fabkury/p64/firmware/assets/fonts/digital-display/Digital-Display-Info.md

# Digital Display
Digital Display is a 19x15 pixel font designed to mimic digital clock fonts while having a bit more flexability in design.

## Author
[VEXED](https://v3x3d.itch.io/)

## Basic Info
- Base Glyph Height: 19px
- Scales: 19, 38, 57, 76, etc.
- Ascender Max: 8px
- Descender Max: 6px

## Kerning
``
``

## License
[Creative Commons Attribution v4.0 International](https://creativecommons.org/licenses/by/4.0/deed.en)

## Supported Glyphs (PNG Order)
``
ABCDEFGH
IJKLMNOP
QRSTUVWX
YZ
abcdefgh
ijklmnop
qrstuvwx
yz
01234567
89
 !"#$%&'
()*+,-./
:;<=>?[]
\^_`{}|~
@∎
ÄÁÀÂÅÃÇç
äáàâåãÑñ
ÏÍÌÎÜÚÙÛ
ïíìîüúùû
ÖÓÒÔÕŸÝỲ
öóòôõÿýỳ
ËÉÈÊëéèê
ÆæßðÐþÞ
¿¡Œœ
``
