fabkury/p64/firmware/assets/fonts/everyday-standard/Everyday-Standard-Info.md

# Everyday Standard
Everyday Standard is a 6pt pixel art font that is part of my Everyday font series. Everyday fonts are designed to be clear and legible at a wide variety of sizes (Everyday Standard's size being the in the middle).

## Author
[VEXED](https://v3x3d.itch.io/)

## Basic Info
- Base Glyph Height: 6px
- Scales: 6, 12, 18, 24, etc
- Ascender Max: 3px
- Descender Max: 2px

## Kerning
None

## License
[Creative Commons Attribution v4.0 International](https://creativecommons.org/licenses/by/4.0/deed.en)

## Supported Glyphs (PNG Order)
``
ABCDEFGH
IJKLMNOP
QRSTUVWX
YZ
abcdefgh
ijklmnop
qrstuvwx
yz
01234567
89
 !"#$%&'
()*+,-./
:;<=>?[]
\^_`{}|~
@∎
ÄÁÀÂÅÃÇç
äáàâåãÑñ
ÏÍÌÎÜÚÙÛ
ïíìîüúùû
ÖÓÒÔÕŸÝỲ
öóòôõÿýỳ
ËÉÈÊëéèê
ÆæßðÐþÞ
¿¡Œœ
АаБбВвГг
ҐґДдЕеЄє
ЖжЗзИиІі
ЇїЙйКкЛл
МмНнОоПп
РрСсТтУу
ФфХхЦцЧч
ШшЩщЬьЮю
ЯяЭэЫыЁё
ЪъӨөӘәҒғ
ҚқҢңҰұҺһ
Үү
Øø
‽⸘ĞğıŞşİ
ĄąĘęŁłŚś
ĆćŻżŹźŃń
ſ́
←↑→↓↔↕
↖↗↘↙
``
