fabkury/p64/firmware/assets/fonts/extra-thick/Extra-Thick-Info.md

# Extra Thick
Extra Thick is a bold 17pt pixel art font designed with very wide and thick looking lettering. 

## Author
[VEXED](https://v3x3d.itch.io/)

## Basic Info
- Base Glyph Height: 17px
- Scales: 17, 34, 51, 68, etc
- Ascender Max: 12px
- Descender Max: 5px

## Kerning
None

## License
[Creative Commons Attribution v4.0 International](https://creativecommons.org/licenses/by/4.0/deed.en)

## Supported Glyphs (PNG Order)
``
ABCDEFGH
IJKLMNOP
QRSTUVWX
YZ
abcdefgh
ijklmnop
qrstuvwx
yz
01234567
89
 !"#$%&'
()*+,-./
:;<=>?[]
\^_`{}|~
@∎
ÄÁÀÂÅÃÇç
äáàâåãÑñ
ÏÍÌÎÜÚÙÛ
ïíìîüúùû
ÖÓÒÔÕŸÝỲ
öóòôõÿýỳ
ËÉÈÊëéèê
ÆæßðÐþÞ
¿¡Œœ
``
