fabkury/p64/firmware/assets/fonts/capital-hill/Capital-Hill-Info.md

# Capital Hill
Capital Hill is a 6pt pixel art font with a focus on capital lettering. Capital Hill's lowercase lettering is styled as scaled down uppercase characters, keeping the two cases subtly distinguished.

## Author
[VEXED](https://v3x3d.itch.io/)

## Basic Info
- Base Glyph Height: 6px
- Scales: 6, 12, 18, 24, etc
- Ascender Max: 3px
- Descender Max: 1px

## Kerning
None

## License
[Creative Commons Attribution v4.0 International](https://creativecommons.org/licenses/by/4.0/deed.en)

## Notes
Turkish support on an all capital lettering font is a touch complex because of the 4 "i" glyphs that exist, please see below for how I have formatted it to work on Capital Hill.

For Capital Hill I have kept the Latin capital set for both uppercase and lowercase consistent. To add the Turkish dotted "i" variations I have made the capital dotted Turkish "i" and the lowercase no dot Turkish "i" both have dots. This allows for accommodation of all 4 glyphs while not compromising on the capital letter style of Capital Hill.

## Supported Glyphs (PNG Order)
``
ABCDEFGH
IJKLMNOP
QRSTUVWX
YZ
abcdefgh
ijklmnop
qrstuvwx
yz
01234567
89
 !"#$%&'
()*+,-./
:;<=>?[]
\^_`{}|~
@∎…‹›
«»■█▀▄©®
═║╗╝╔╚╣╠
╩╦╬─│┐┘┌
└┤├┴┬┼§¶
¤¢¥£€₽฿₣
°×÷≡µ±ƒ¬
Ææ¿¡¦░▒▓
ºª¹²³½⅔¾
¼⅓⅕⅖⅗⅘⅙⅚
⅛⅜⅝⅞“”‘’
ÄÁÀÂÅÃÇç
äáàâåãÑñ
ÏÍÌÎÜÚÙÛ
ïíìîüúùû
ÖÓÒÔÕŸÝỲ
öóòôõÿýỳ
ËÉÈÊëéèê
ŒœßðÐþÞ
АаБбВвГг
ҐґДдЕеЄє
ЖжЗзИиІі
ЇїЙйКкЛл
МмНнОоПп
РрСсТтУу
ФфХхЦцЧч
ШшЩщЬьЮю
ЯяЭэЫыЁё
ЪъӨөӘәҒғ
ҚқҢңҰұҺһ
Үү
Øø
‽⸘ĞğıŞşİ
ĄąĘęŁłŚś
ĆćŻżŹźŃń
ſ́
←↑→↓↔↕
↖↗↘↙
``
