fabkury/p64/docs/images/photos/p64-brick-wall-analogue-clock.jpg

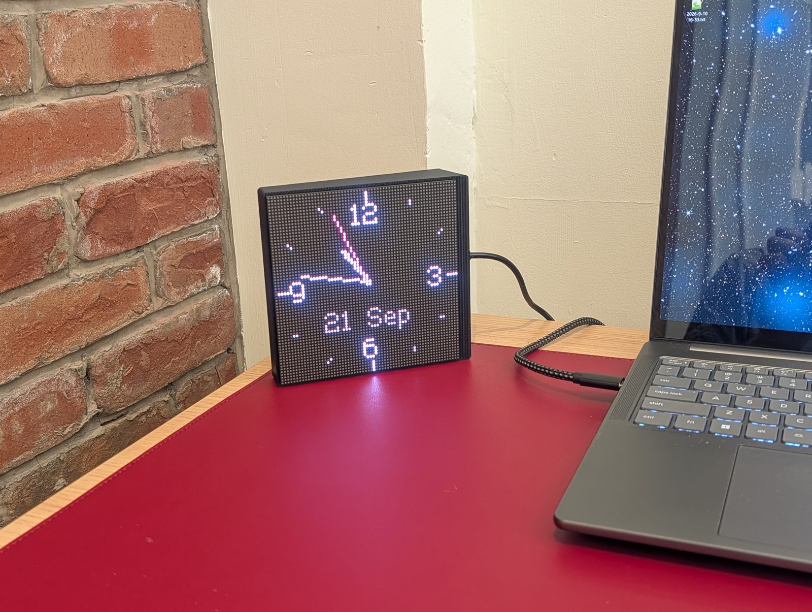
docs/images/photos/p64-brick-wall-analogue-clock.jpg
