fabkury/p64/docs/images/photos/p64-brick-wall-artwork-dark.jpg

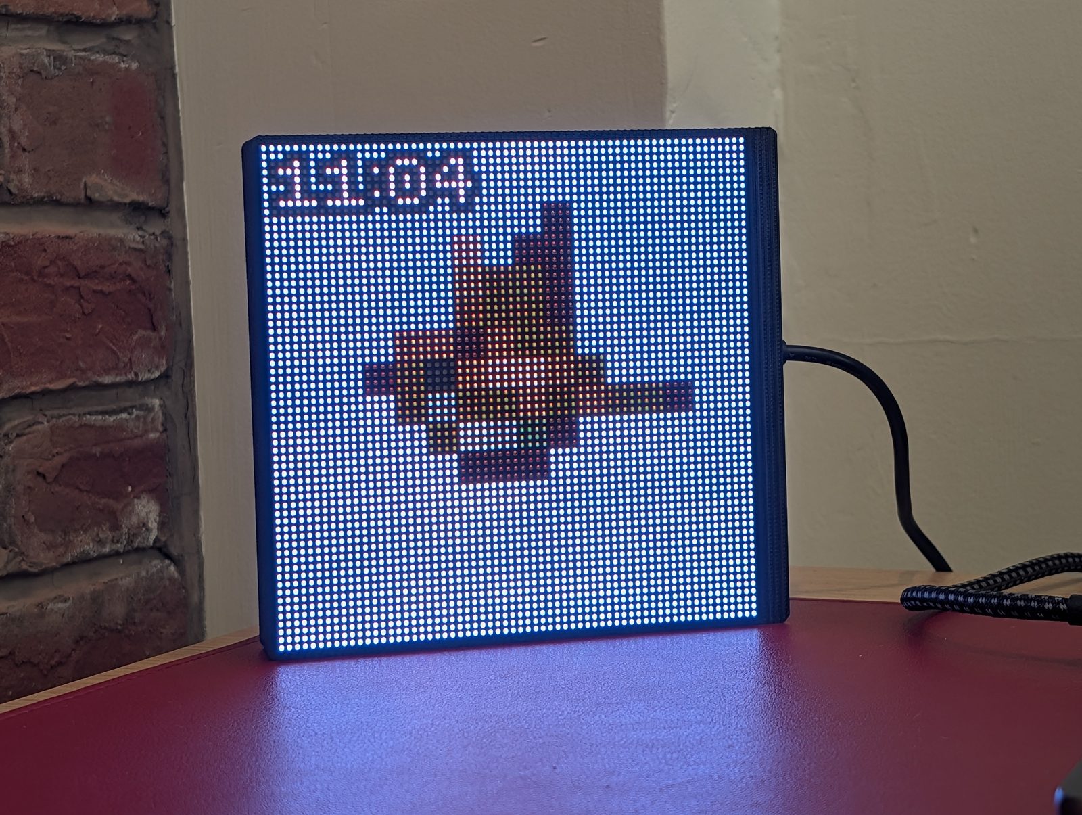
docs/images/photos/p64-brick-wall-artwork-dark.jpg
