fabkury/p64/docs/images/photos/p64-brick-wall-artwork-green.jpg

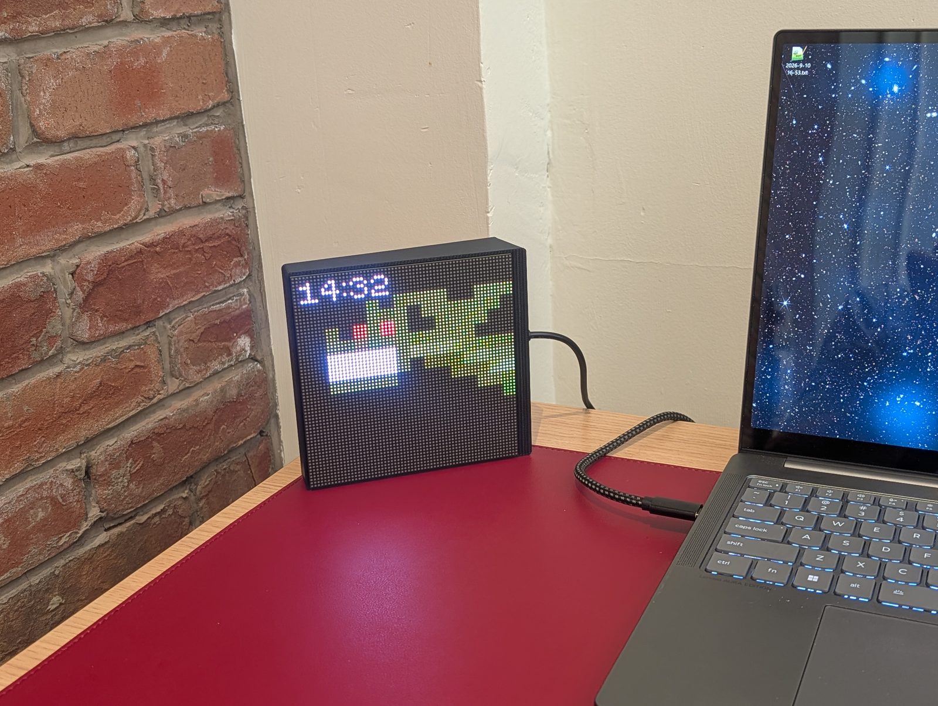
docs/images/photos/p64-brick-wall-artwork-green.jpg
