fabkury/p64/docs/images/photos/p64-brick-wall-heart.jpg

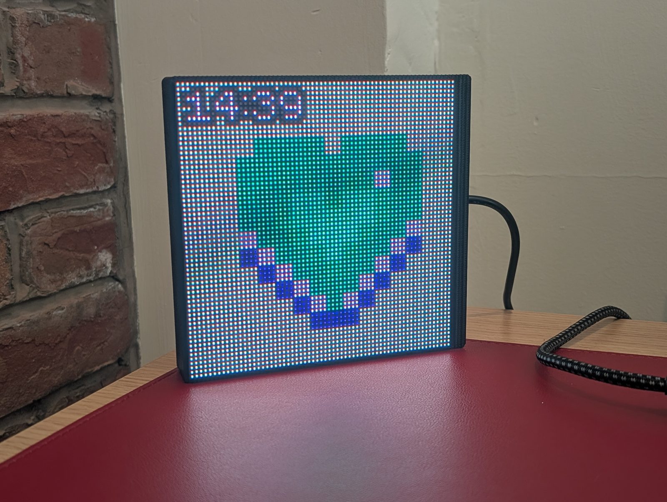
docs/images/photos/p64-brick-wall-heart.jpg
