fabkury/p64/docs/images/photos/p64-brick-wall-jellyfish.jpg

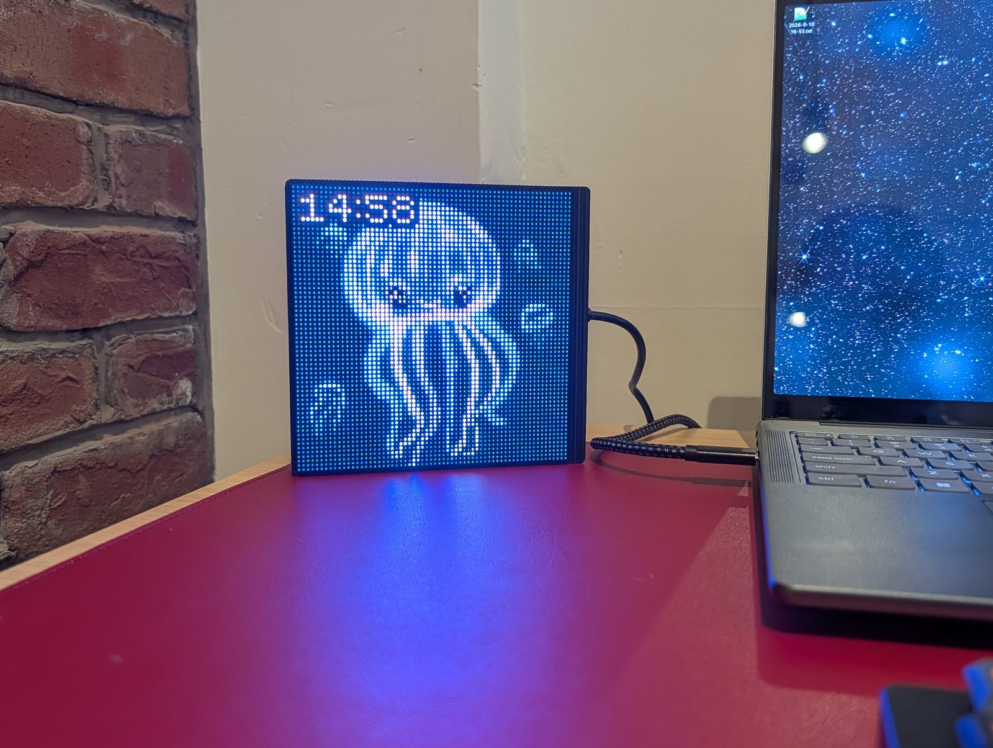
docs/images/photos/p64-brick-wall-jellyfish.jpg
