fabkury/p64/docs/images/photos/p64-shell-back.jpg

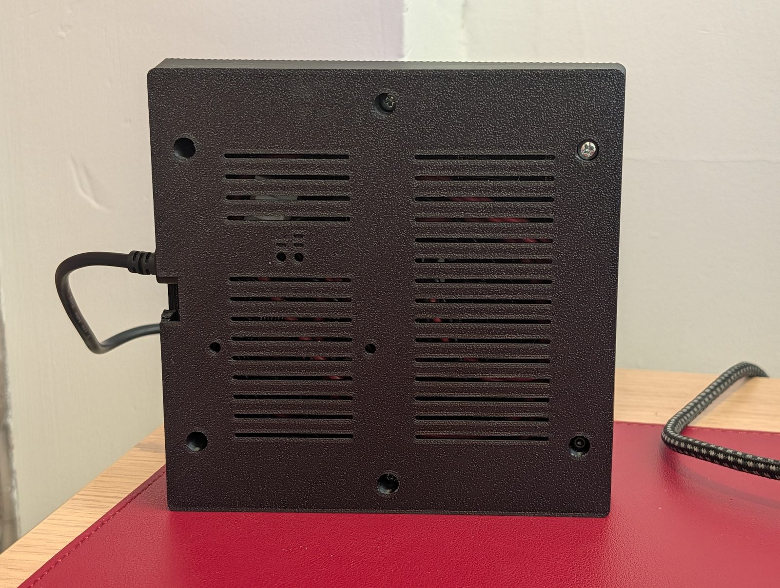
docs/images/photos/p64-shell-back.jpg
