fabkury/p64/docs/images/photos/p64-shell-side.jpg

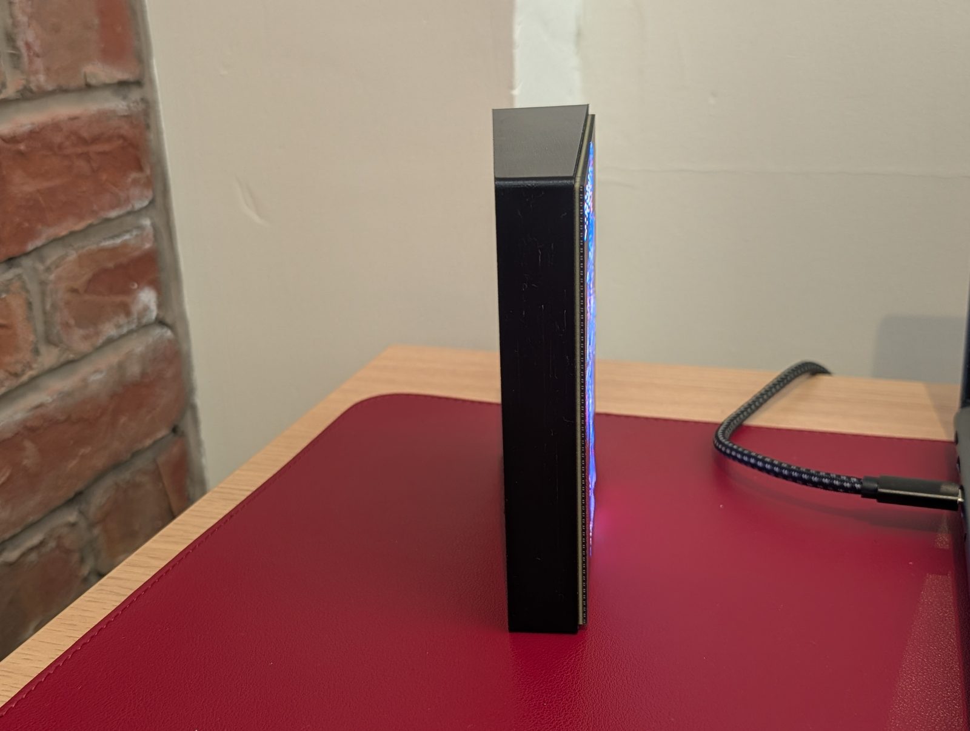
docs/images/photos/p64-shell-side.jpg
