fabkury/p64/docs/images/photos/p64-shell-v1-back-vents.jpg

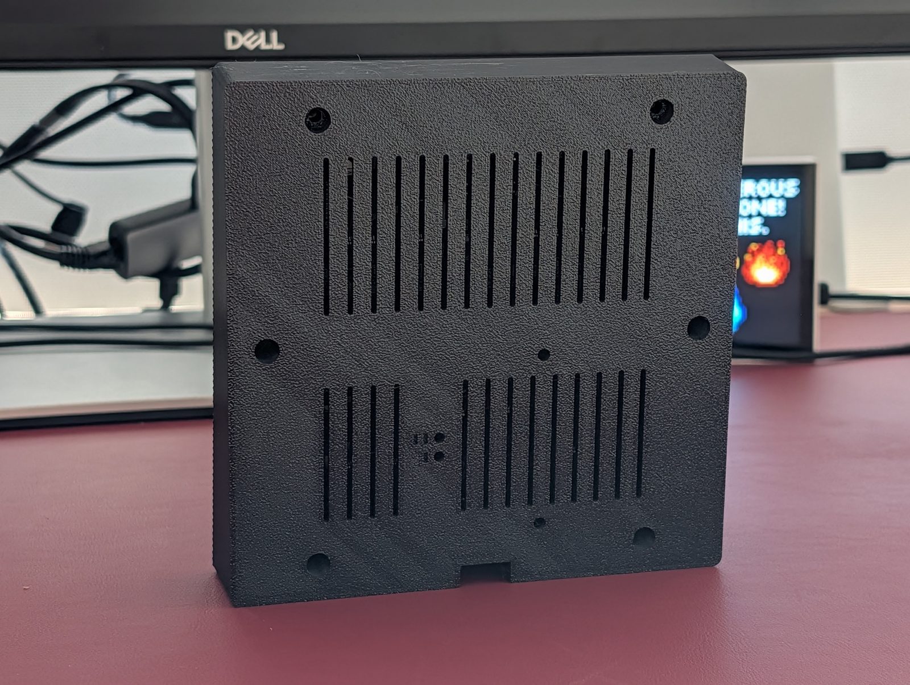
docs/images/photos/p64-shell-v1-back-vents.jpg
