fabkury/p64/firmware/docs/design/air-widget/european.png

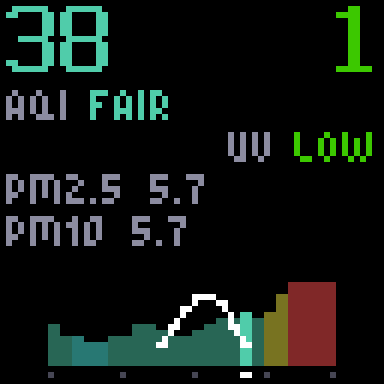
firmware/docs/design/air-widget/european.png
