fabkury/p64/firmware/docs/design/air-widget/good.png

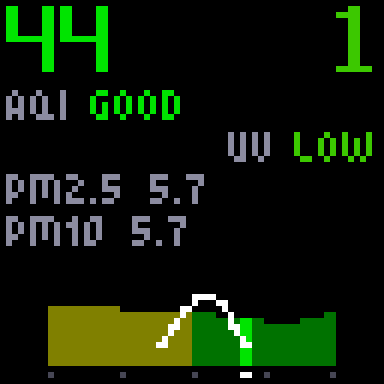
firmware/docs/design/air-widget/good.png
