fabkury/p64/firmware/docs/design/air-widget/moderate.png

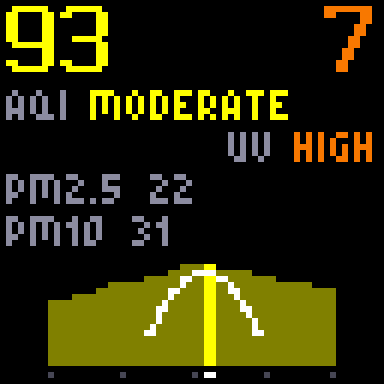
firmware/docs/design/air-widget/moderate.png
