fabkury/p64/firmware/docs/design/air-widget/no-location.png

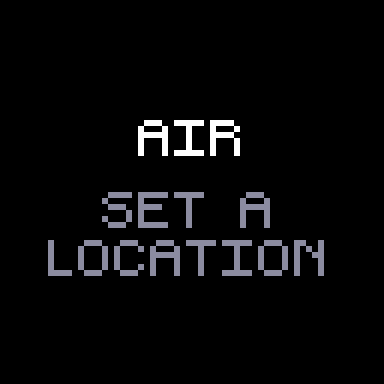
firmware/docs/design/air-widget/no-location.png
