fabkury/p64/firmware/docs/design/air-widget/sensitive.png

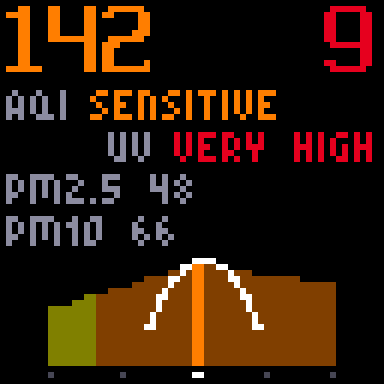
firmware/docs/design/air-widget/sensitive.png
