fabkury/p64/firmware/docs/design/air-widget/sheet.png

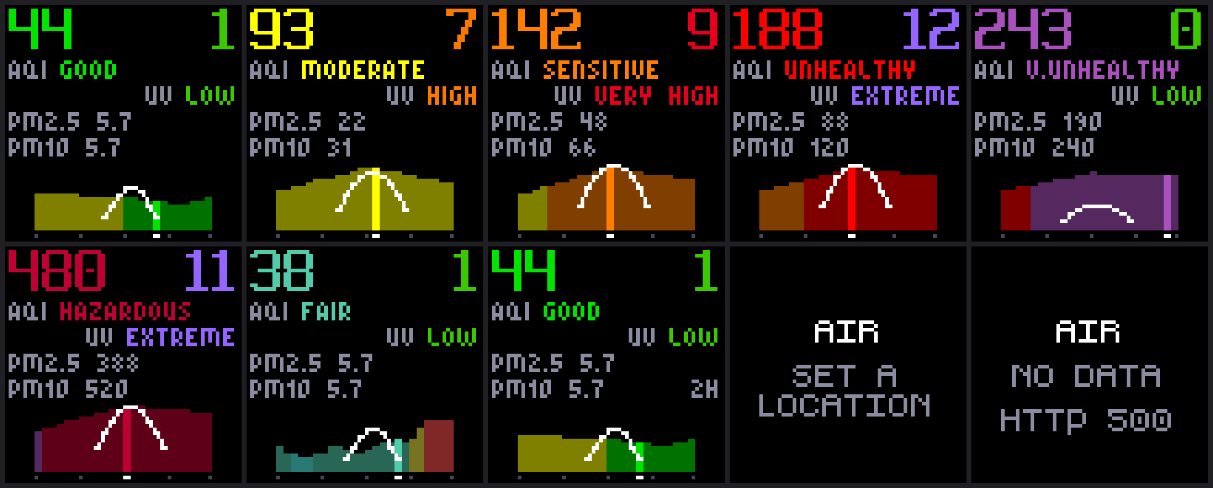
firmware/docs/design/air-widget/sheet.png
