fabkury/p64/firmware/docs/design/air-widget/unhealthy.png

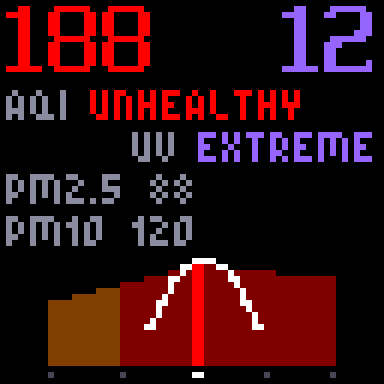
firmware/docs/design/air-widget/unhealthy.png
