fabkury/p64/firmware/docs/design/air-widget/very-unhealthy.png

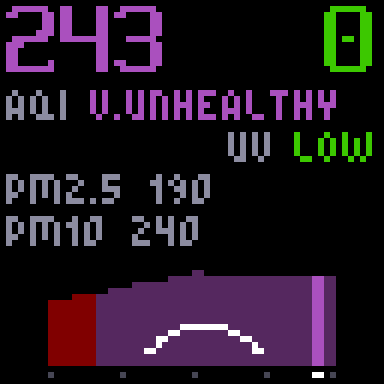
firmware/docs/design/air-widget/very-unhealthy.png
