fabkury/p64/firmware/docs/design/clock-candidates/aquarium-moments.png

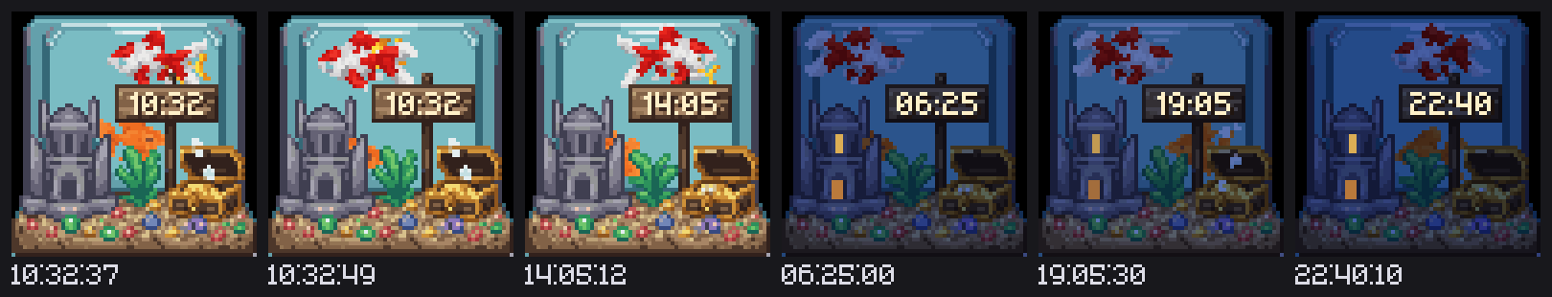
firmware/docs/design/clock-candidates/aquarium-moments.png
