fabkury/p64/firmware/docs/design/clock-candidates/aquarium-night@8x.gif

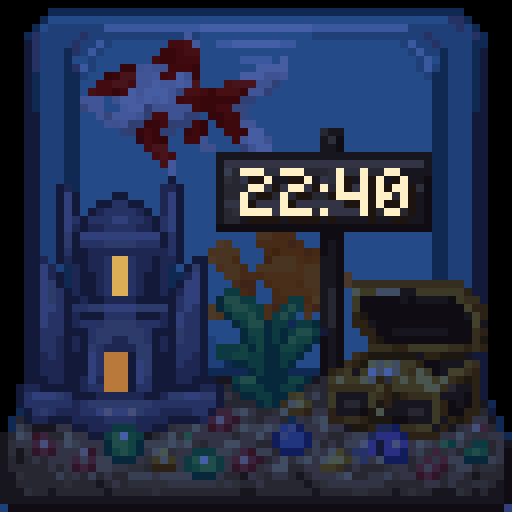
firmware/docs/design/clock-candidates/aquarium-night@8x.gif
