fabkury/p64/firmware/docs/design/clock-candidates/aquarium@8x.gif

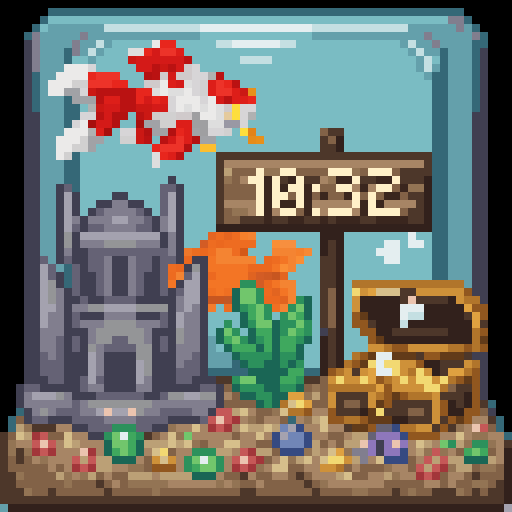
firmware/docs/design/clock-candidates/aquarium@8x.gif
