fabkury/p64/firmware/docs/design/clock-candidates/aquarium@8x.png

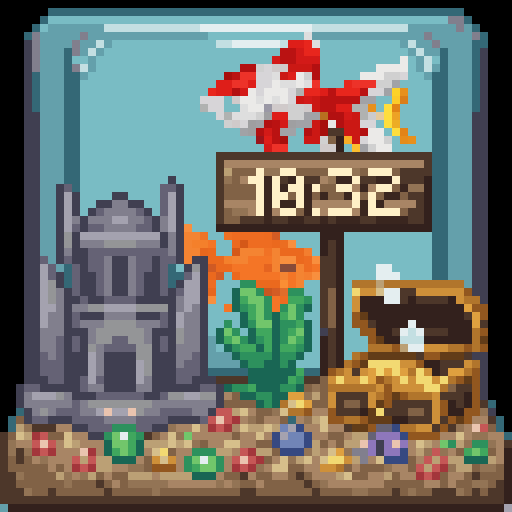
firmware/docs/design/clock-candidates/aquarium@8x.png
