fabkury/p64/firmware/docs/design/clock-candidates/bracket-moments.png

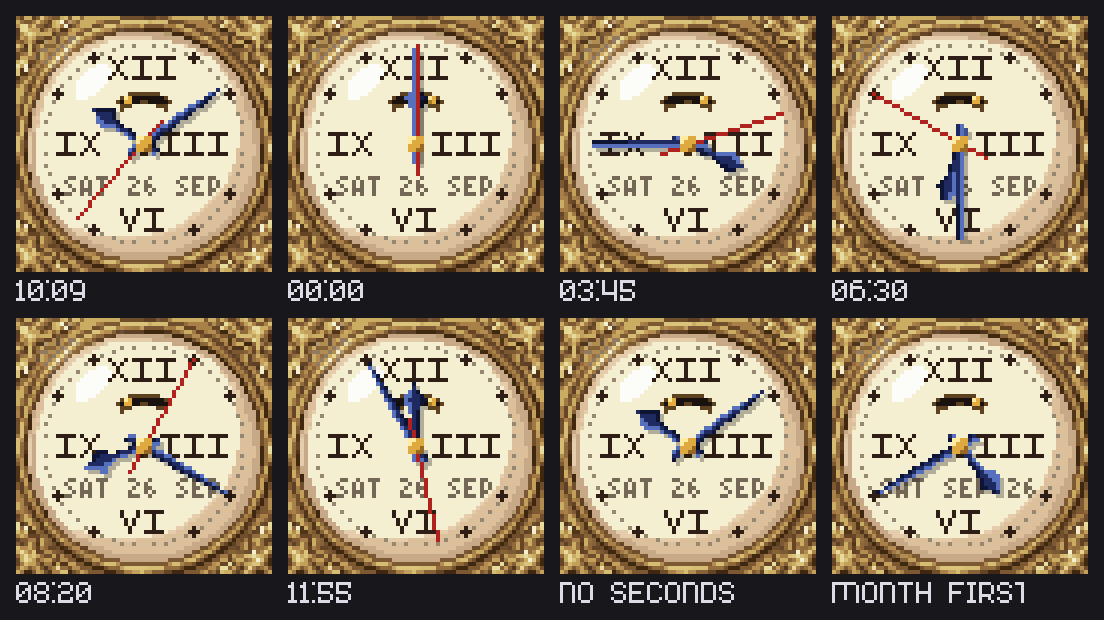
firmware/docs/design/clock-candidates/bracket-moments.png
