fabkury/p64/firmware/docs/design/clock-candidates/contact-sheet.png

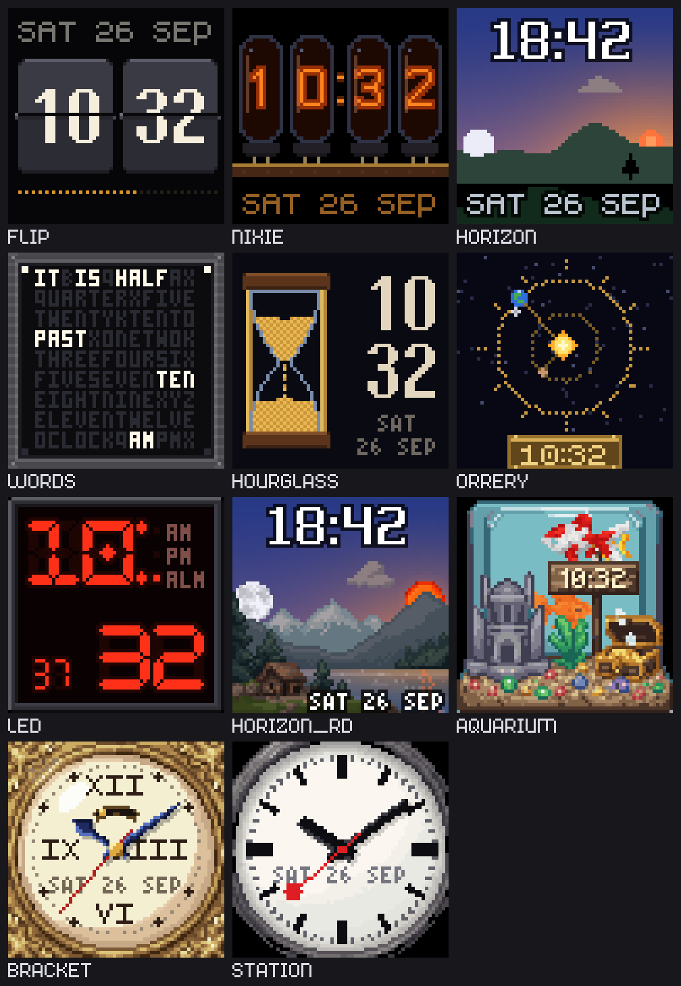
firmware/docs/design/clock-candidates/contact-sheet.png
