fabkury/p64/firmware/docs/design/clock-candidates/horizon-day.png

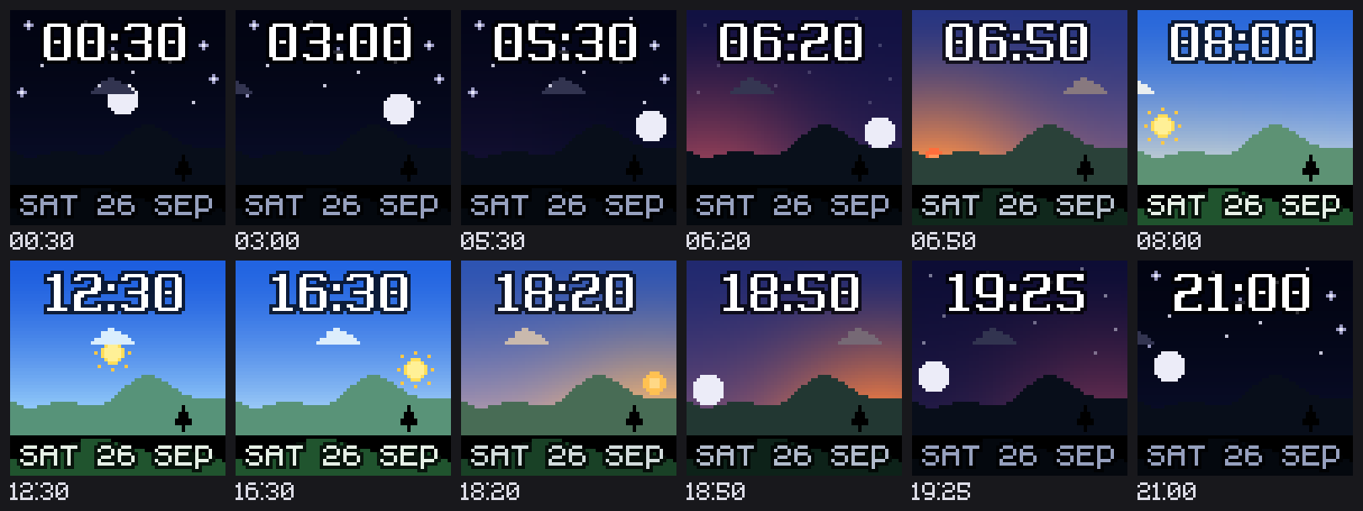
firmware/docs/design/clock-candidates/horizon-day.png
