fabkury/p64/firmware/docs/design/clock-candidates/horizon-variants.png

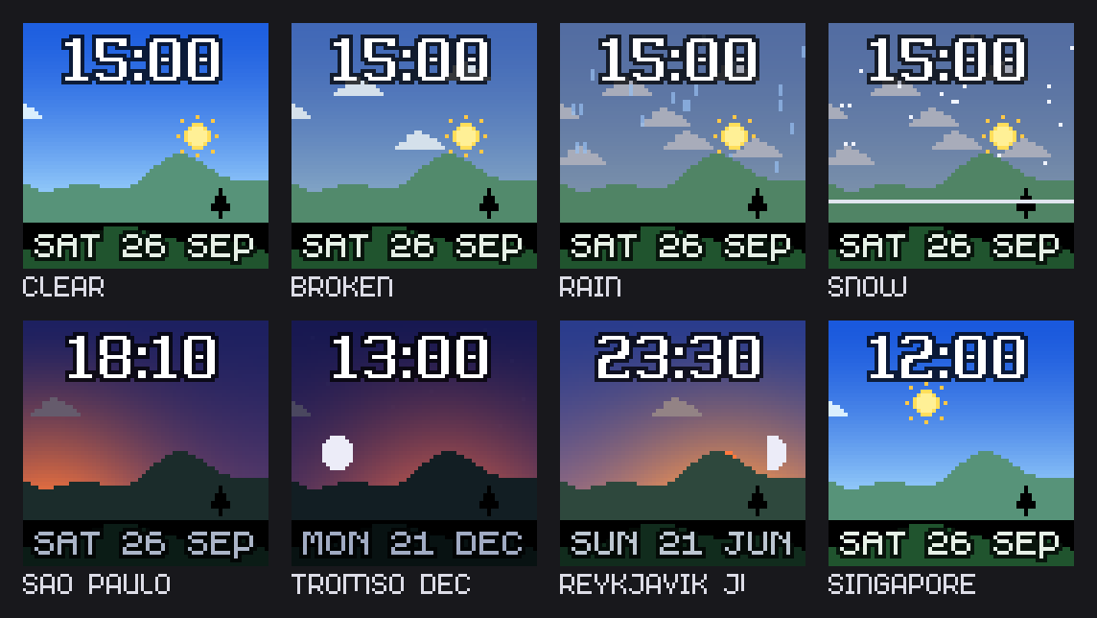
firmware/docs/design/clock-candidates/horizon-variants.png
