fabkury/p64/firmware/docs/design/clock-candidates/horizon@8x.png

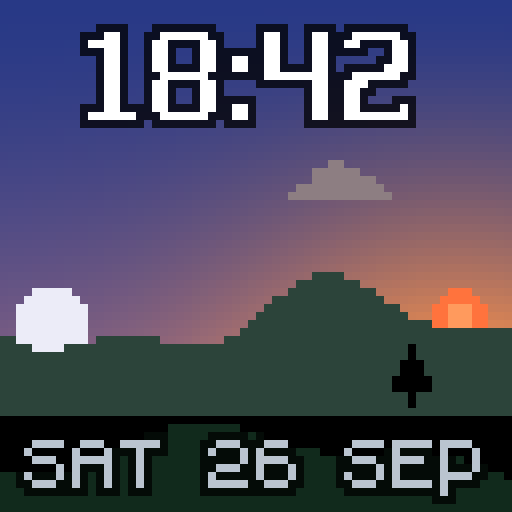
firmware/docs/design/clock-candidates/horizon@8x.png
