fabkury/p64/firmware/docs/design/clock-candidates/horizon_rd-day.png

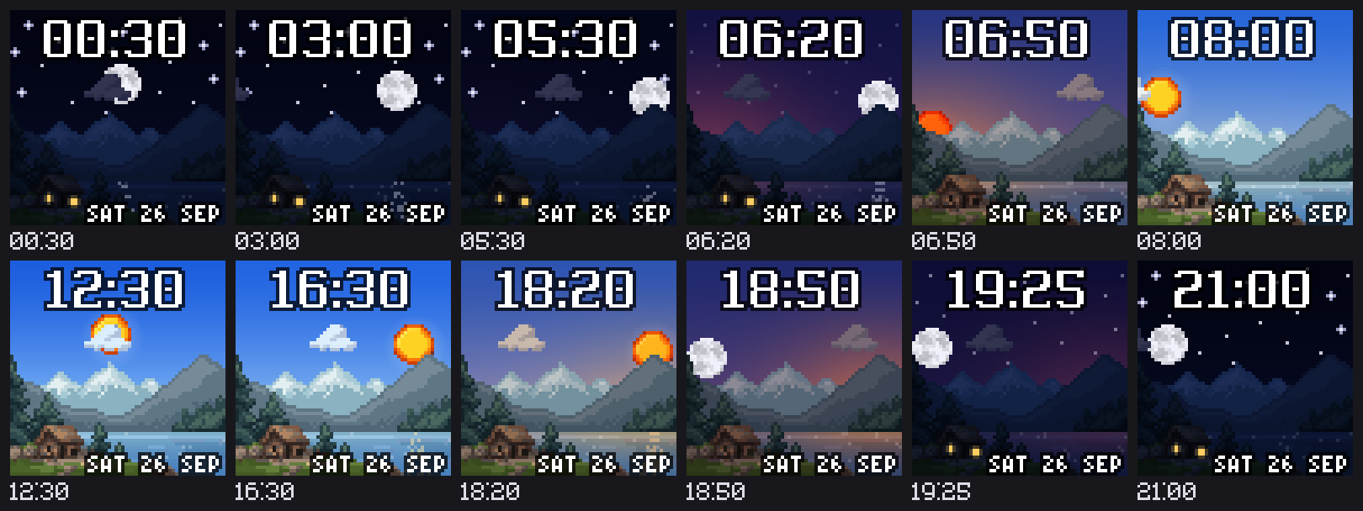
firmware/docs/design/clock-candidates/horizon_rd-day.png
