fabkury/p64/firmware/docs/design/clock-candidates/horizon_rd-variants.png

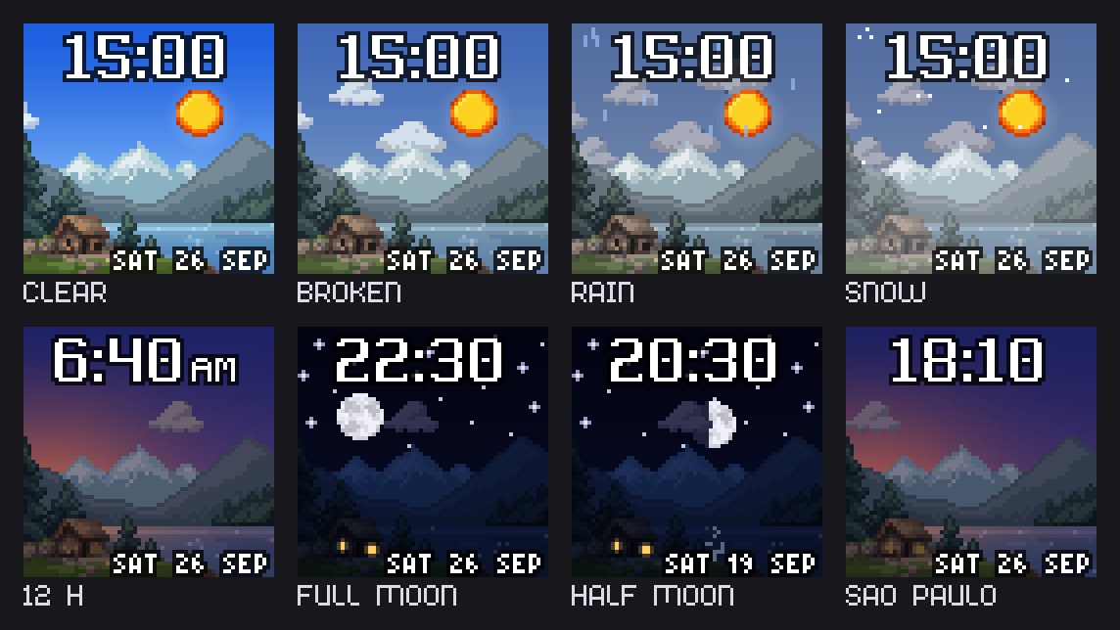
firmware/docs/design/clock-candidates/horizon_rd-variants.png
