fabkury/p64/firmware/docs/design/clock-candidates/horizon_rd@8x.gif

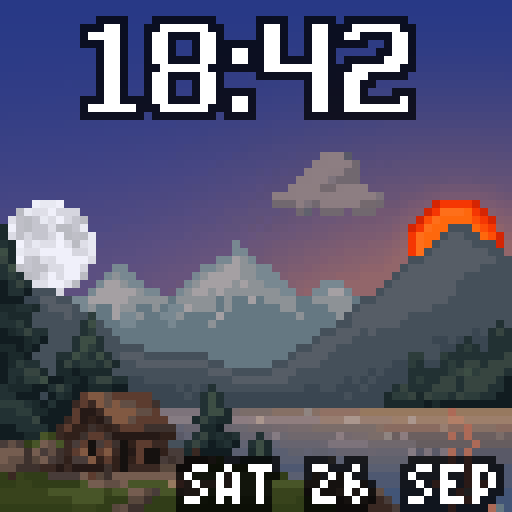
firmware/docs/design/clock-candidates/horizon_rd@8x.gif
