fabkury/p64/firmware/docs/design/clock-candidates/hourglass-moments.png

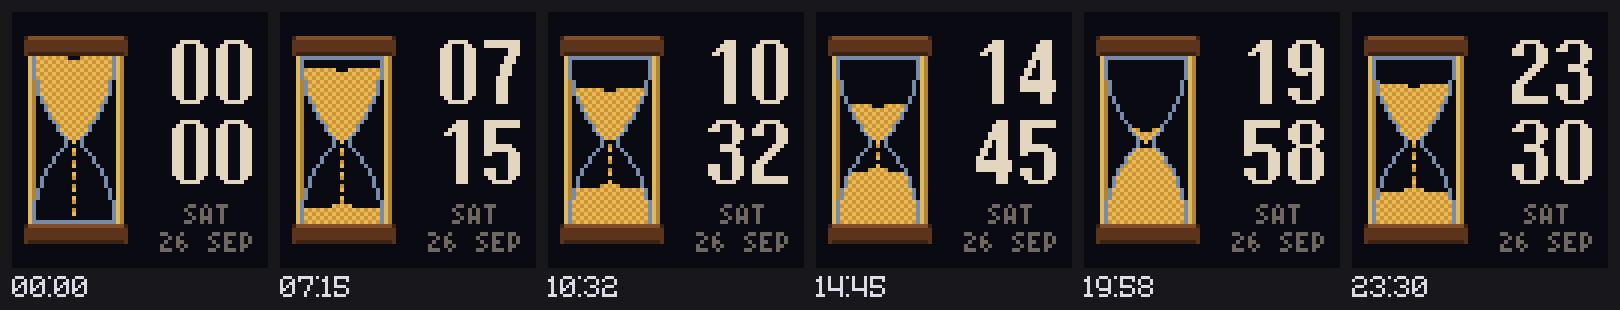
firmware/docs/design/clock-candidates/hourglass-moments.png
