fabkury/p64/firmware/docs/design/clock-candidates/hourglass@8x.gif

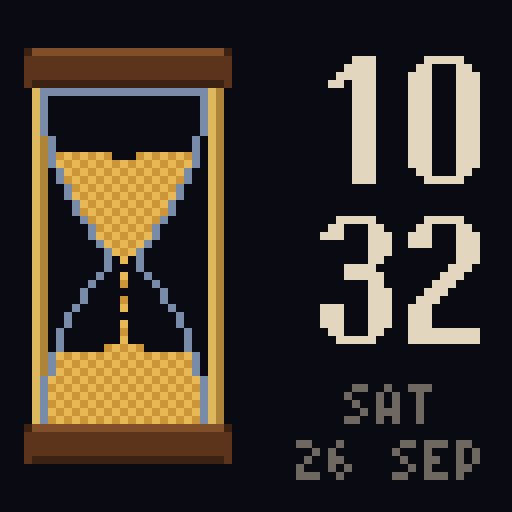
firmware/docs/design/clock-candidates/hourglass@8x.gif
