fabkury/p64/firmware/docs/design/clock-candidates/led-styles.png

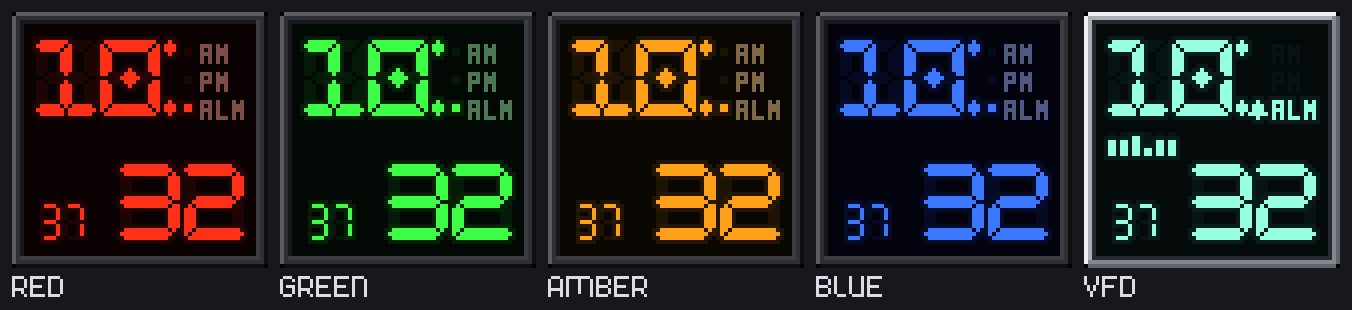
firmware/docs/design/clock-candidates/led-styles.png
