fabkury/p64/firmware/docs/design/clock-candidates/led-vfd@8x.gif

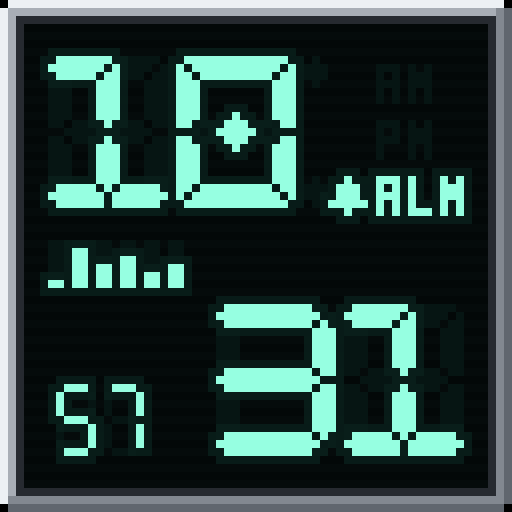
firmware/docs/design/clock-candidates/led-vfd@8x.gif
