fabkury/p64/firmware/docs/design/clock-candidates/led@8x.gif

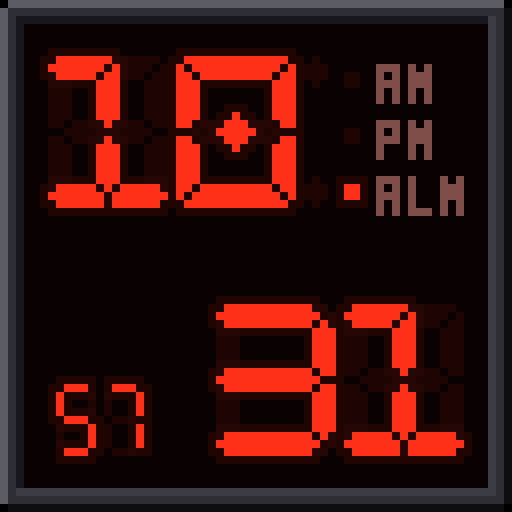
firmware/docs/design/clock-candidates/led@8x.gif
