fabkury/p64/firmware/docs/design/clock-candidates/led@8x.png

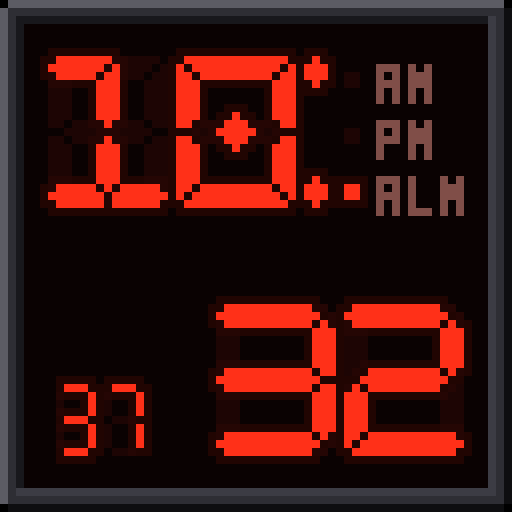
firmware/docs/design/clock-candidates/led@8x.png
