fabkury/p64/firmware/docs/design/clock-candidates/nixie@8x.png

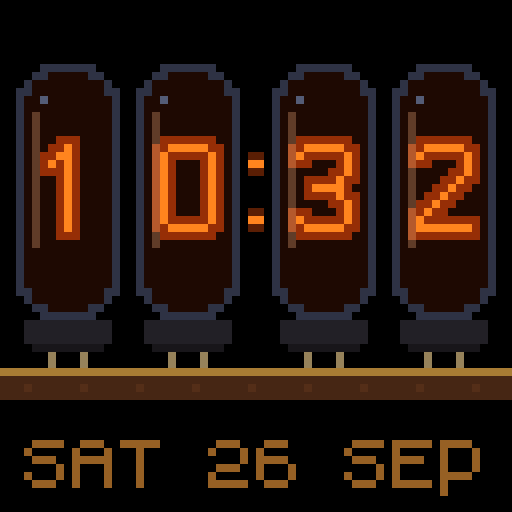
firmware/docs/design/clock-candidates/nixie@8x.png
