fabkury/p64/firmware/docs/design/clock-candidates/orrery@8x.gif

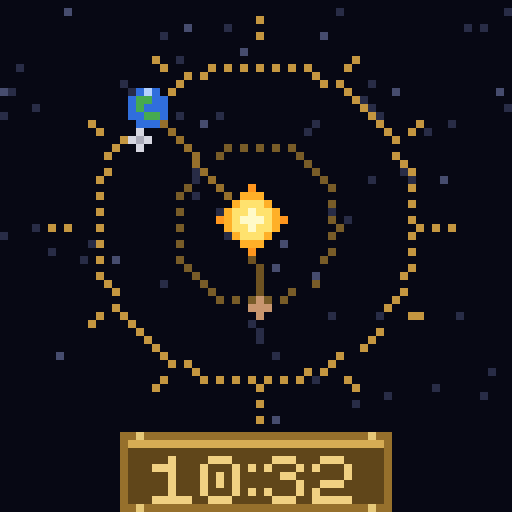
firmware/docs/design/clock-candidates/orrery@8x.gif
