fabkury/p64/firmware/docs/design/clock-candidates/station-glint.png

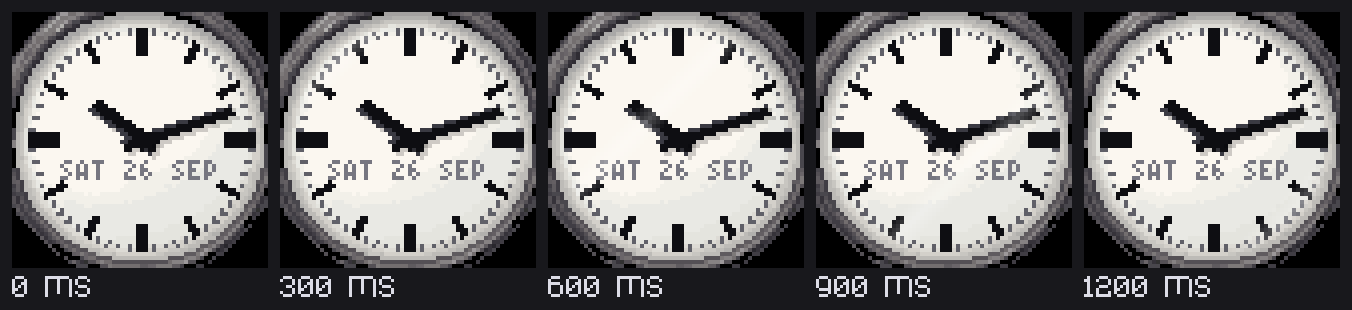
firmware/docs/design/clock-candidates/station-glint.png
