fabkury/p64/firmware/docs/design/clock-candidates/station@8x.gif

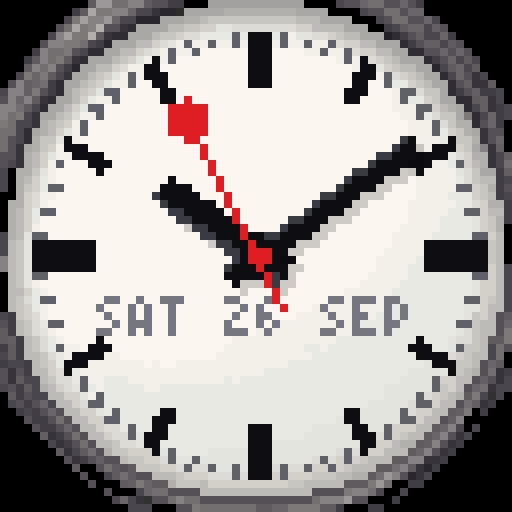
firmware/docs/design/clock-candidates/station@8x.gif
