fabkury/p64/firmware/docs/design/clock-candidates/words-moments.png

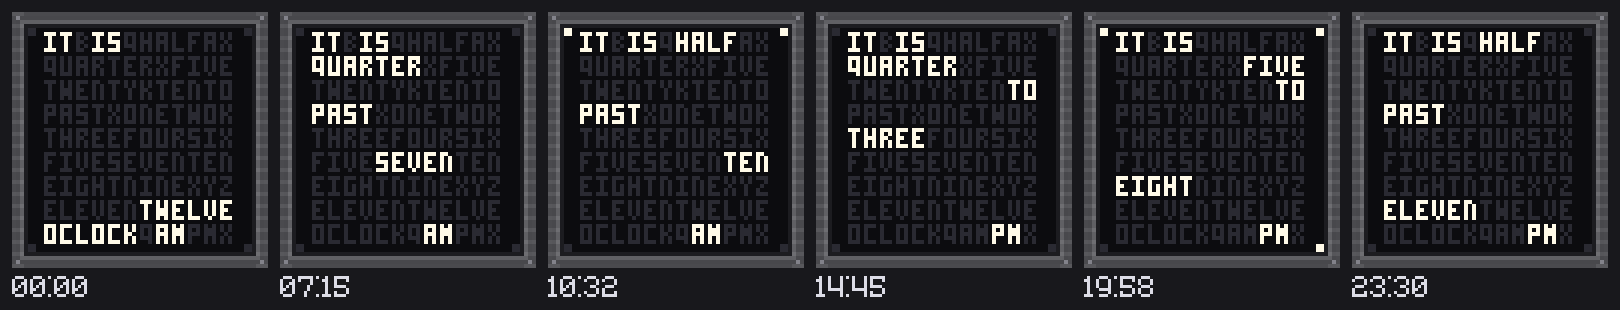
firmware/docs/design/clock-candidates/words-moments.png
