fabkury/p64/firmware/docs/design/clock-candidates/words@8x.png

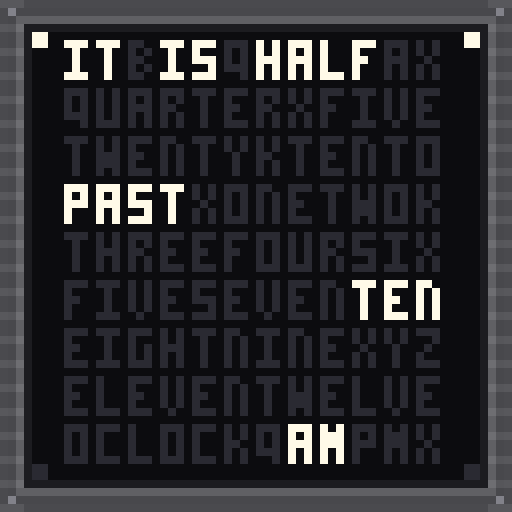
firmware/docs/design/clock-candidates/words@8x.png
