fabkury/p64/enclosure/output/p64a/v7a/render_assembly.png

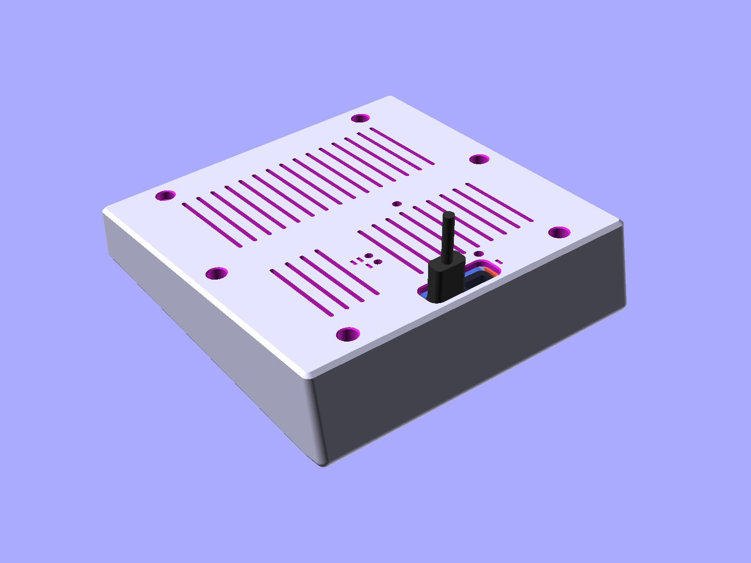
enclosure/output/p64a/v7a/render_assembly.png
