fabkury/p64/enclosure/output/p64b/v7b/render_assembly.png

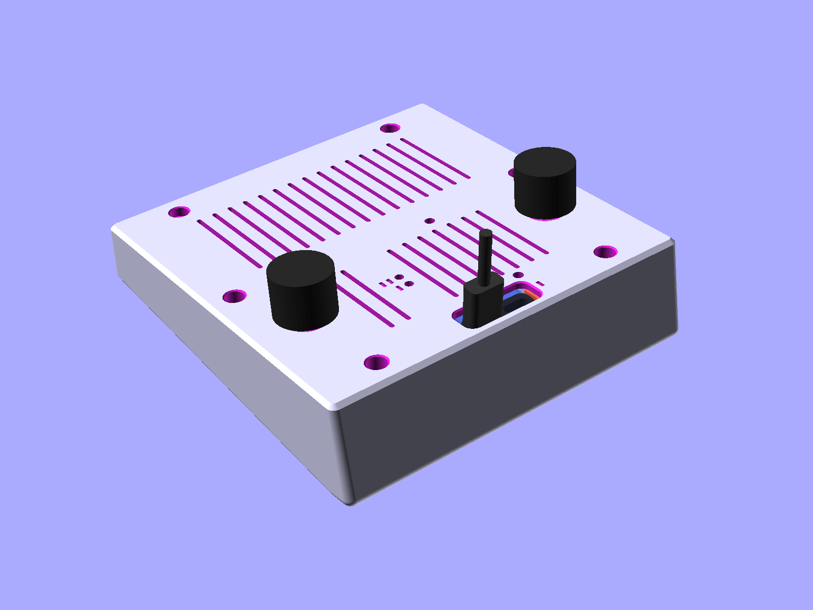
enclosure/output/p64b/v7b/render_assembly.png
