fabkury/p64/enclosure/input/usb-c-90-degree-adapter/PXL_20260919_152802345 - with measures.jpeg

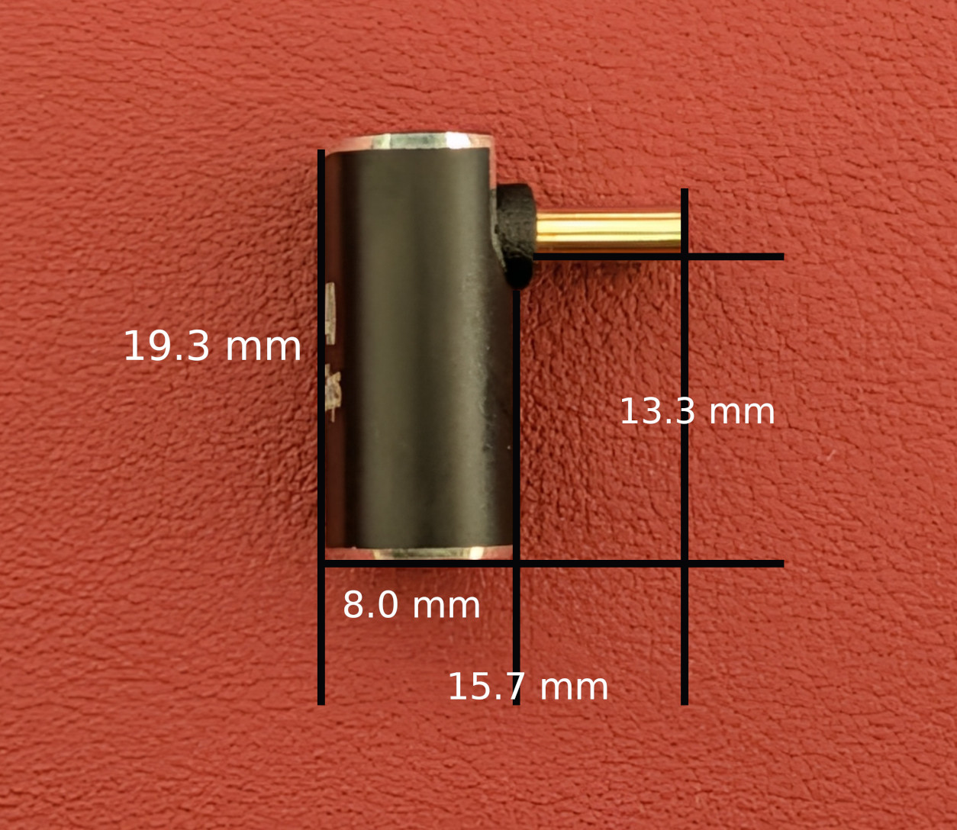
enclosure/input/usb-c-90-degree-adapter/PXL_20260919_152802345 - with measures.jpeg
