fabkury/p64/firmware/tests/host/corpus/apng_rgba_128.png

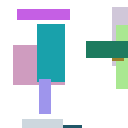
firmware/tests/host/corpus/apng_rgba_128.png
