fabkury/p64/firmware/tests/host/corpus/png_rgb_256.png

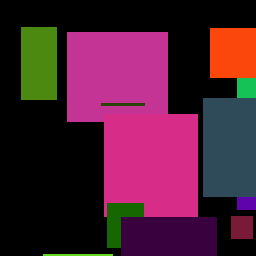
firmware/tests/host/corpus/png_rgb_256.png
