fabkury/p64/firmware/tests/host/corpus/png_rgba_128.png

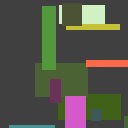
firmware/tests/host/corpus/png_rgba_128.png
