fabkury/p64/firmware/tests/host/corpus/webp_anim_lossy_128.webp

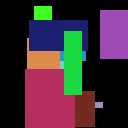
firmware/tests/host/corpus/webp_anim_lossy_128.webp
