fabkury/p64/firmware/docs/design/air-widget/hazardous.png

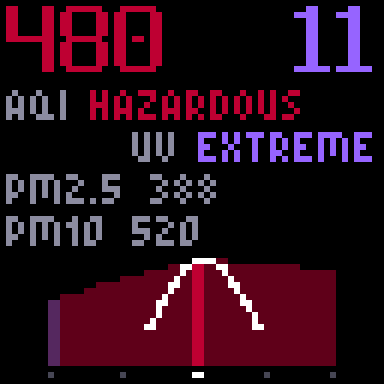
firmware/docs/design/air-widget/hazardous.png
