fabkury/p64/firmware/main/show_core.hpp

// p64 -- the show core: the Animation show, the Widget and Stream states, history,
// playsets and their channels, the auto-swap, pause, play-this, status screens and the
// stream takeover (spec 4.5 to 6, 8.3), as code with no ESP-IDF include. Everything it
// does to the world goes through ShowEnv; show.cpp is the shell that owns the command
// queue, the task and the device's ShowEnv, and tests/host/unit/show.cpp drives the core
// with a fake one through whole scenarios. Review of 2026-09-22, proposal P-T1.
//
// Not thread-safe: the shell calls it from the show loop, and the API's readers under the
// shell's mutex. The three atomics the player's overlay hook reads are the exception.
#pragma once

#include <cstdarg>
#include <cstddef>
#include <cstdint>
#include <memory>
#include <string>
#include <vector>

#include "cJSON.h"
#include "loader.hpp"
#include "p64/content/history.hpp"
#include "p64/content/playset.hpp"
#include "p64/content/provider.hpp"
#include "p64/content/scheduler.hpp"
#include "p64/gfx/frame.hpp"
#include "p64/makapix/makapix.hpp"
#include "p64/net/wifi.hpp"
#include "p64/playback/artwork.hpp"
#include "p64/playback/frame_source.hpp"
#include "p64/stream/stream.hpp"
#include "p64/system/settings.hpp"
#include "show_rules.hpp"

namespace p64::show {

// The world as the core sees it. The device's implementation lives in show.cpp.
class ShowEnv {
 public:
  virtual ~ShowEnv() = default;

  // Time, chance, settings.
  virtual int64_t now_us() = 0;
  virtual uint32_t random() = 0;
  virtual std::shared_ptr<const system::Settings> settings() = 0;
  virtual void persist_main_state(system::MainState state) = 0;
  virtual void persist_active_playset(const std::string &name) = 0;
  virtual bool load_playset(const std::string &name, content::Playset &out, std::string &error) = 0;

  // The panel.
  virtual void play(std::shared_ptr<playback::FrameSource> source) = 0;
  virtual std::shared_ptr<playback::FrameSource> static_frame(const char *name, const gfx::Frame &frame) = 0;
  // `face` overrides the clock's configured face for this source (-1 = the setting).
  virtual std::shared_ptr<playback::FrameSource> widget(system::WidgetKind kind, int face) = 0;
  virtual const char *widget_name(system::WidgetKind kind) = 0;
  virtual std::shared_ptr<playback::FrameSource> stream_source() = 0;
  virtual void stream_wake() = 0;
  virtual stream::Status stream_status() = 0;
  struct RenderTotals {
    uint32_t frames = 0, late = 0, skipped = 0;
  };
  virtual RenderTotals render_totals() = 0;

  // The card (through the loader task: results come back as on_loaded/on_scanned).
  virtual uint32_t load(const std::string &path, gfx::Rgb background) = 0;
  virtual void scan(uint32_t generation, const content::Playset &playset) = 0;
  virtual bool card_mounted() = 0;
  virtual std::string storage_root() = 0;
  virtual std::string animations_dir() = 0;
  virtual std::string downloads_dir() = 0;

  // Makapix Club, beyond what the content provider interface covers (ADR 0012): the
  // pairing screens read its state and code, the Followed built-in is generated by the
  // server. Channel artworks of any provider go through content::providers.
  virtual makapix::Status makapix_status() = 0;
  virtual bool makapix_paired() = 0;
  virtual bool makapix_play_followed(std::string &error) = 0;

  // Network, notifications, log.
  virtual net::wifi::Status wifi_status() = 0;
  // A firmware update as the show sees it (from the OTA status); the Update screen follows
  // it (spec 6.4).
  struct UpdateState {
    enum class Phase : uint8_t { None, Downloading, Verifying, Ready, Failed };
    Phase phase = Phase::None;
    std::string version;
    int percent = -1;  // -1 while the size is unknown
    std::string error;
  };
  virtual UpdateState update_state() = 0;
  virtual void playback_swapped(int32_t history_position) = 0;  // the PlaybackSwapped event
  virtual void notify_web() = 0;
  virtual void vlog(char level, const char *format, va_list args) = 0;  // 'E', 'W', 'I', 'D'
};

namespace core {

// The runtime of one channel of the active playset: a local folder (provider null) or a
// channel of a content provider (Makapix Club, the private area; ADR 0012).
struct ChannelRuntime {
  content::ChannelSpec spec;
  content::Provider *provider = nullptr;  // null: a local channel
  content::LocalEntries entries;          // local channels
  content::ProviderItems items;           // provider channels: pickable now (at hand and within the size limit)
  uint32_t listed = 0;                    // provider channels: entries in the provider's index
  uint32_t last_refresh = 0;              // provider channels: epoch seconds of the last listing, 0 never
  uint32_t oversized = 0;                 // provider channels: listed then but outside the size limits
  uint32_t unchecked = 0;                 // provider channels: entries a post-load file check has not reached
  uint32_t available = 0;                 // entries neither missing nor rejected (local) or pickable (provider)
  std::string status;                     // "" when the channel can supply artworks, else why not
};

struct Pick {
  uint32_t generation = 0;  // the playset generation it was made against
  int channel = -1;
  int entry = -1;     // index in the channel's pickable list
  uint32_t pool = 0;  // pickable entries in the channel at pick time
  content::Provider *provider = nullptr;  // the channel's provider (null: local)
  content::ProviderItem item = {};        // provider channels: the item picked
  std::string path;
  std::string name;
  std::string channel_name;
};

struct Pending {
  enum class Purpose : uint8_t { None, Navigate, PlayThis, Resume } purpose = Purpose::None;
  uint32_t load_id = 0;
  int direction = 0;  // navigation: -1 previous, +1 next, 0 exact
  content::HistoryItem item;
};

enum class Screen : uint8_t { None, Pairing, Paired, Connected, Setup, Update };

// Everything the show knows. One value, so a test resets it by assignment and reads it.
struct State {
  content::Playset playset;
  std::vector<ChannelRuntime> channels;
  // Bumped whenever the channel list or its counts change: the web UI refetches
  // /api/v1/channels when the number in the status document moves.
  uint32_t channels_version = 0;
  content::Scheduler scheduler;
  content::History history;
  uint32_t generation = 0;  // bumps per scan request; results carry it back

  bool paused = false;
  int64_t swap_at_us = 0;      // when the current item went up
  int64_t boot_until_us = 0;   // the boot animation holds the panel until then
  std::shared_ptr<playback::Artwork> current;  // the artwork on the panel (null: status screen or pause)
  std::string status_reason;   // the "no artwork" reason on the panel ("" when none)
  bool status_pending = false; // ...decided while the boot animation ran: drawn at its end if still nothing
  std::string last_error;      // the last load or activation failure, for the UI
  Screen screen = Screen::None;  // a status screen that holds the panel
  int64_t screen_until_us = 0;   // when a timed screen ends (0 = until its cause ends)
  // The "connected" screen (rules::connected_screen): an IP landed and the decision
  // waits for the boot animation; once up, the screen yields to a ready artwork after a
  // short minimum stay.
  bool connected_pending = false;
  int64_t connected_yield_us = 0;
  // Time-to-first-artwork (spec 15.1, acceptance 18.8): when the first artwork of this
  // boot went up (0 = none yet); the status document reports it next to boot_until_us.
  int64_t first_artwork_us = 0;
  // The setup pages: on the Setup screen, or in place of the "no artwork" screen.
  bool setup_pages_up = false;
  int setup_page = 0;
  int64_t setup_page_at_us = 0;  // when the next page is due
  ShowEnv::UpdateState update_drawn;  // what the Update screen shows
  std::shared_ptr<playback::FrameSource> widget;  // the widget on the panel (Widget state or an interlude)
  bool widget_up = false;
  system::WidgetKind widget_kind = system::WidgetKind::Clock;
  int widget_face = -1;                // the clock face on the panel when overridden (an interlude)
  uint8_t last_interlude_face = 255;   // the last random face drawn, never drawn twice running
  bool want_widget = false;  // the Widget state waits for the boot animation
  rules::Stage<std::shared_ptr<playback::FrameSource>> stage;  // on the panel, and behind a stream
  bool stream_active = false;  // stream frames are arriving (StreamStarted .. StreamEnded)
  bool want_stream = false;    // a takeover waits for the boot animation or a screen

  Pick prepared_pick;
  std::shared_ptr<playback::Artwork> prepared;
  uint32_t prepared_load_id = 0;
  bool want_prepared_now = false;
  uint32_t prepare_failures = 0;
  Pending pending;

  bool scan_running = false;
  bool scan_again = false;
  bool activate_after_scan = false;
  int64_t rescan_due_us = 0;
  int64_t retry_at_us = 0;
  uint32_t swaps = 0;
  uint32_t load_failures = 0;
  uint32_t last_scan_ms = 0;
};

// Sets the world and the scratch frame the status screens are drawn into, and resets the
// state (the tests call it before each scenario).
void init(ShowEnv &env, gfx::Frame &scratch);
const State &state();

// The boot animation holds the panel for `boot_ms` (spec 15.1); `source` shows meanwhile.
void boot(std::shared_ptr<playback::FrameSource> source, uint32_t boot_ms);
// Activates the saved playset (`saved_name`, "" when none) or the spec's fallback, and
// enters the saved main state.
void restore(const std::string &saved_name);

// Commands (from the API, the site, the IMU).
void next();
void previous();
void go_to(size_t history_index);
void pause();
void resume();
void reset_timer();
void refresh();
// Play this widget as an interlude now (one auto-swap slot, enters history); ignored
// outside the Animation show and under a stream.
void interlude(system::WidgetKind kind);
// Play-this: a file on the card ("" provider), or a download of a provider (its id and
// the item's id, -1 for a plain URL).
void play_file(const std::string &path, const std::string &provider, int32_t item_id, const std::string &name);
void activate(const std::string &name);
void activate_transient(const content::Playset &playset);

// Events and results.
void on_loaded(std::unique_ptr<loader::LoadResult> result);
void on_scanned(std::unique_ptr<loader::ScanResult> result);
void card_changed();
void files_changed();
void settings_changed();
void provider_changed();  // a provider's channel index or cache changed
void makapix_state(makapix::State state);
void wifi_connected();
void stream_started();
void stream_ended();

// Periodic work, and how long the loop may sleep before it has something to do.
void tick();
int64_t wait_us();

// Readers.
bool overlay_allowed();  // an artwork is up, no stream, the show runs (any task)
bool is_paused();
int32_t current_post_id();  // the Makapix post on the panel, -1 otherwise (Makapix presence and likes)
const std::string &active_playset_name();
cJSON *status_json();
cJSON *channels_json();
cJSON *history_json();

}  // namespace core
}  // namespace p64::show
