fabkury/p64/firmware/components/p64_system/src/settings_model.cpp

// The settings document itself: defaults, clamping and the JSON form (spec section 16).
// No ESP-IDF includes: host-tested (tests/host/unit/system.cpp). The store (NVS, the
// shared view, change events) is settings.cpp.
#include "p64/system/settings.hpp"

#include <algorithm>
#include <cstring>
#include <limits>

#include "cJSON.h"

namespace p64::system {
namespace {

template <typename T>
T clamp_to(T v, T lo, T hi) {
  return v < lo ? lo : (v > hi ? hi : v);
}

bool valid_device_name(const std::string &n) {
  if (n.size() > 16) return false;
  if (!n.empty() && (n.front() == '-' || n.back() == '-')) return false;
  for (char c : n) {
    if (!((c >= 'a' && c <= 'z') || (c >= '0' && c <= '9') || c == '-')) return false;
  }
  return true;
}

// --- JSON helpers -------------------------------------------------------------

cJSON *obj(cJSON *parent, const char *name) {
  cJSON *o = cJSON_AddObjectToObject(parent, name);
  return o;
}

void put_rgb(cJSON *parent, const char *name, gfx::Rgb c) {
  cJSON *o = cJSON_AddObjectToObject(parent, name);
  cJSON_AddNumberToObject(o, "r", c.r);
  cJSON_AddNumberToObject(o, "g", c.g);
  cJSON_AddNumberToObject(o, "b", c.b);
}

const cJSON *sub(const cJSON *parent, const char *name) {
  const cJSON *o = cJSON_GetObjectItemCaseSensitive(parent, name);
  return (o && cJSON_IsObject(o)) ? o : nullptr;
}

// Numbers are clamped into the target type's range first, so an out-of-range value
// like 999 for a uint8_t clamps to 255 instead of wrapping.
template <typename T>
void get_num(const cJSON *o, const char *name, T &out) {
  if (!o) return;
  const cJSON *v = cJSON_GetObjectItemCaseSensitive(o, name);
  if (!v || !cJSON_IsNumber(v)) return;
  double d = v->valuedouble;
  const double lo = static_cast<double>(std::numeric_limits<T>::min());
  const double hi = static_cast<double>(std::numeric_limits<T>::max());
  if (d < lo) d = lo;
  if (d > hi) d = hi;
  out = static_cast<T>(d);
}

void get_bool(const cJSON *o, const char *name, bool &out) {
  if (!o) return;
  const cJSON *v = cJSON_GetObjectItemCaseSensitive(o, name);
  if (v && cJSON_IsBool(v)) out = cJSON_IsTrue(v);
}

void get_str(const cJSON *o, const char *name, std::string &out, size_t max_len) {
  if (!o) return;
  const cJSON *v = cJSON_GetObjectItemCaseSensitive(o, name);
  if (v && cJSON_IsString(v) && v->valuestring) out = std::string(v->valuestring).substr(0, max_len);
}

void get_rgb(const cJSON *o, const char *name, gfx::Rgb &out) {
  const cJSON *c = sub(o, name);
  if (!c) return;
  int r = out.r, g = out.g, b = out.b;
  get_num(c, "r", r);
  get_num(c, "g", g);
  get_num(c, "b", b);
  out = gfx::Rgb{static_cast<uint8_t>(clamp_to(r, 0, 255)), static_cast<uint8_t>(clamp_to(g, 0, 255)),
                 static_cast<uint8_t>(clamp_to(b, 0, 255))};
}

// Enum by name, tolerant of unknown values (left unchanged).
template <typename E>
void get_enum(const cJSON *o, const char *name, E &out, const char *const *names, size_t count) {
  if (!o) return;
  const cJSON *v = cJSON_GetObjectItemCaseSensitive(o, name);
  if (!v || !cJSON_IsString(v) || !v->valuestring) return;
  for (size_t i = 0; i < count; ++i) {
    if (std::strcmp(v->valuestring, names[i]) == 0) {
      out = static_cast<E>(i);
      return;
    }
  }
}

const char *const kPanelModes[] = {"quality", "photo"};
const char *const kMainStates[] = {"animation_show", "widget", "stream"};
const char *const kPickModes[] = {"random", "recency"};
const char *const kChannelSelects[] = {"stochastic", "swrr"};
const char *const kCorners[] = {"top_left", "top_right", "bottom_left", "bottom_right", "top_center", "bottom_center"};
const char *const kWidgets[] = {"clock", "weather", "temperature", "air"};
const char *const kClockFaces[] = {"digital", "analogue", "flip", "nixie", "horizon", "words", "hourglass", "orrery", "led", "horizon_rd", "aquarium", "bracket", "station"};
const char *const kLedStyles[] = {"red", "green", "amber", "blue", "vfd"};

}  // namespace

void Settings::clamp() {
  brightness = clamp_to<uint8_t>(brightness, 1, 255);
  brightness_ceiling = clamp_to<uint8_t>(brightness_ceiling, 1, 255);
  night.start_minutes = clamp_to<uint16_t>(night.start_minutes, 0, 24 * 60 - 1);
  night.end_minutes = clamp_to<uint16_t>(night.end_minutes, 0, 24 * 60 - 1);
  if (!gfx::valid_rotation(rotation)) rotation = 90;
  gain_r = clamp_to<uint8_t>(gain_r, 50, 100);
  gain_g = clamp_to<uint8_t>(gain_g, 50, 100);
  gain_b = clamp_to<uint8_t>(gain_b, 50, 100);
  // 0 is off; anything else is a length between 1 and 7 s (decided 2026-09-26).
  if (boot_animation_ms != 0) boot_animation_ms = clamp_to<uint16_t>(boot_animation_ms, 1000, 7000);
  if (auto_swap_seconds != 0) auto_swap_seconds = clamp_to<uint32_t>(auto_swap_seconds, 5, 86400);
  clock.scale = clamp_to<uint8_t>(clock.scale, 1, 3);
  clock_overlay.border_opacity = clamp_to<uint8_t>(clock_overlay.border_opacity, 1, 255);
  weather.refresh_minutes = clamp_to<uint16_t>(weather.refresh_minutes, 10, 180);
  if (weather.latitude < -90 || weather.latitude > 90 || weather.longitude < -180 || weather.longitude > 180) {
    weather.location_set = false;
    weather.latitude = weather.longitude = 0;
  }
  temperature.offset_temperature = clamp_to<int8_t>(temperature.offset_temperature, -10, 10);
  temperature.offset_humidity = clamp_to<int8_t>(temperature.offset_humidity, -10, 10);
  // 0 is never; anything else is a median gap of 5 min to a day (ADR 0014).
  if (interlude_clock != 0) interlude_clock = clamp_to<uint16_t>(interlude_clock, 5, 1440);
  if (interlude_weather != 0) interlude_weather = clamp_to<uint16_t>(interlude_weather, 5, 1440);
  if (interlude_temperature != 0) interlude_temperature = clamp_to<uint16_t>(interlude_temperature, 5, 1440);
  if (interlude_air != 0) interlude_air = clamp_to<uint16_t>(interlude_air, 5, 1440);
  stream_silence_ms = clamp_to<uint32_t>(stream_silence_ms, 500, 60000);
  if (ddp_port == 0) ddp_port = 4048;
  if (raw_udp_port == 0) raw_udp_port = 4064;
  tap_sensitivity = clamp_to<uint8_t>(tap_sensitivity, 1, 10);
  if (!valid_device_name(device_name)) device_name.clear();
  if (timezone.empty()) timezone = "UTC";
  if (ntp_server.empty()) ntp_server = "pool.ntp.org";
  if (card_root.empty() || card_root.front() != '/') card_root = "/p64";
  downloads_cap_mb = clamp_to<uint16_t>(downloads_cap_mb, 16, 1024);
  makapix_refresh_seconds = clamp_to<uint32_t>(makapix_refresh_seconds, 60, 86400);
  channel_cache_size = clamp_to<uint16_t>(channel_cache_size, 32, 4096);
  makapix_min_side = snap_min_side(makapix_min_side);
  makapix_max_side = snap_max_side(makapix_max_side);
  // apply_json refuses a minimum above the maximum; a stored pair can only conflict
  // through a hand-edited document, and then the maximum wins.
  if (makapix_min_side > makapix_max_side) makapix_min_side = makapix_max_side;
  cache_retention_days = clamp_to<uint16_t>(cache_retention_days, 1, 365);
}

const char *clock_face_name(ClockFace face) {
  const int i = static_cast<int>(face);
  return (i >= 0 && i < kClockFaceCount) ? kClockFaces[i] : kClockFaces[0];
}

std::string Settings::hostname() const { return device_name.empty() ? "p64" : "p64-" + device_name; }

std::string Settings::to_json() const {
  cJSON *root = cJSON_CreateObject();
  cJSON *d = obj(root, "display");
  cJSON_AddNumberToObject(d, "brightness", brightness);
  cJSON_AddNumberToObject(d, "brightness_ceiling", brightness_ceiling);
  cJSON *n = obj(d, "night");
  cJSON_AddBoolToObject(n, "enabled", night.enabled);
  cJSON_AddNumberToObject(n, "start_minutes", night.start_minutes);
  cJSON_AddNumberToObject(n, "end_minutes", night.end_minutes);
  cJSON_AddNumberToObject(n, "brightness", night.brightness);
  cJSON_AddStringToObject(d, "panel_mode", kPanelModes[static_cast<int>(panel_mode)]);
  cJSON_AddNumberToObject(d, "rotation", rotation);
  cJSON_AddBoolToObject(d, "rotation_auto", rotation_auto);
  cJSON_AddBoolToObject(d, "mirror", mirror);
  put_rgb(d, "background", background);
  cJSON *g = obj(d, "gains");
  cJSON_AddNumberToObject(g, "r", gain_r);
  cJSON_AddNumberToObject(g, "g", gain_g);
  cJSON_AddNumberToObject(g, "b", gain_b);
  cJSON_AddNumberToObject(d, "boot_animation_ms", boot_animation_ms);

  cJSON *s = obj(root, "show");
  cJSON_AddStringToObject(s, "main_state", kMainStates[static_cast<int>(main_state)]);
  cJSON_AddNumberToObject(s, "auto_swap_seconds", auto_swap_seconds);
  cJSON_AddStringToObject(s, "pick_mode", kPickModes[static_cast<int>(pick_mode)]);
  cJSON_AddStringToObject(s, "channel_select", kChannelSelects[static_cast<int>(channel_select)]);
  cJSON *co = obj(s, "clock_overlay");
  cJSON_AddBoolToObject(co, "enabled", clock_overlay.enabled);
  cJSON_AddStringToObject(co, "font", clock_overlay.font.c_str());
  cJSON_AddStringToObject(co, "corner", kCorners[static_cast<int>(clock_overlay.corner)]);
  cJSON_AddBoolToObject(co, "h24", clock_overlay.h24);
  put_rgb(co, "colour", clock_overlay.colour);
  cJSON_AddBoolToObject(co, "border", clock_overlay.border);
  put_rgb(co, "border_colour", clock_overlay.border_colour);
  cJSON_AddNumberToObject(co, "border_opacity", clock_overlay.border_opacity);

  cJSON *w = obj(root, "widgets");
  cJSON_AddStringToObject(w, "widget", kWidgets[static_cast<int>(widget)]);
  cJSON *ip = obj(w, "interlude_minutes");
  cJSON_AddNumberToObject(ip, "clock", interlude_clock);
  cJSON_AddNumberToObject(ip, "weather", interlude_weather);
  cJSON_AddNumberToObject(ip, "temperature", interlude_temperature);
  cJSON_AddNumberToObject(ip, "air", interlude_air);
  cJSON_AddBoolToObject(w, "interlude_random_clock_face", interlude_random_clock_face);

  cJSON *ck = obj(root, "clock");
  cJSON_AddStringToObject(ck, "face", kClockFaces[static_cast<int>(clock.face)]);
  cJSON_AddStringToObject(ck, "led_style", kLedStyles[static_cast<int>(clock.led_style)]);
  cJSON_AddStringToObject(ck, "font", clock.font.c_str());
  cJSON_AddNumberToObject(ck, "scale", clock.scale);
  cJSON_AddBoolToObject(ck, "seconds", clock.seconds);
  cJSON_AddBoolToObject(ck, "blink_colon", clock.blink_colon);
  cJSON_AddBoolToObject(ck, "h24", clock.h24);
  cJSON_AddStringToObject(ck, "date_order", clock.month_first ? "month_day" : "day_month");
  put_rgb(ck, "colour", clock.colour);
  put_rgb(ck, "background", clock.background);

  cJSON *we = obj(root, "weather");
  cJSON_AddBoolToObject(we, "location_set", weather.location_set);
  cJSON_AddNumberToObject(we, "latitude", weather.latitude);
  cJSON_AddNumberToObject(we, "longitude", weather.longitude);
  cJSON_AddStringToObject(we, "units", weather.imperial ? "imperial" : "metric");
  cJSON_AddNumberToObject(we, "refresh_minutes", weather.refresh_minutes);

  cJSON *ai = obj(root, "air");
  cJSON_AddStringToObject(ai, "index", air.european ? "european" : "us");

  cJSON *te = obj(root, "temperature");
  cJSON_AddNumberToObject(te, "offset_temperature", temperature.offset_temperature);
  cJSON_AddNumberToObject(te, "offset_humidity", temperature.offset_humidity);
  cJSON_AddBoolToObject(te, "trend", temperature.trend);

  cJSON *st = obj(root, "stream");
  cJSON_AddBoolToObject(st, "takeover", stream_takeover);
  cJSON_AddNumberToObject(st, "silence_ms", stream_silence_ms);
  cJSON_AddBoolToObject(st, "ddp_enabled", ddp_enabled);
  cJSON_AddNumberToObject(st, "ddp_port", ddp_port);
  cJSON_AddBoolToObject(st, "raw_udp_enabled", raw_udp_enabled);
  cJSON_AddNumberToObject(st, "raw_udp_port", raw_udp_port);

  cJSON *in = obj(root, "inputs");
  cJSON_AddBoolToObject(in, "tap_enabled", tap_enabled);
  cJSON_AddNumberToObject(in, "tap_sensitivity", tap_sensitivity);
  cJSON_AddBoolToObject(in, "encoders_enabled", encoders_enabled);
  cJSON_AddBoolToObject(in, "encoders_swap", encoders_swap);
  cJSON_AddBoolToObject(in, "encoders_invert", encoders_invert);

  cJSON *net = obj(root, "network");
  cJSON_AddStringToObject(net, "device_name", device_name.c_str());
  cJSON_AddStringToObject(net, "timezone", timezone.c_str());
  cJSON_AddStringToObject(net, "ntp_server", ntp_server.c_str());

  cJSON *sto = obj(root, "storage");
  cJSON_AddStringToObject(sto, "card_root", card_root.c_str());
  cJSON_AddNumberToObject(sto, "downloads_cap_mb", downloads_cap_mb);

  cJSON *mk = obj(root, "makapix");
  cJSON_AddNumberToObject(mk, "refresh_seconds", makapix_refresh_seconds);
  cJSON_AddNumberToObject(mk, "channel_cache_size", channel_cache_size);
  cJSON_AddNumberToObject(mk, "min_size", makapix_min_side);
  cJSON_AddNumberToObject(mk, "max_size", makapix_max_side);
  cJSON_AddNumberToObject(mk, "cache_retention_days", cache_retention_days);

  cJSON *up = obj(root, "updates");
  cJSON_AddBoolToObject(up, "auto_check", auto_update_check);

  char *text = cJSON_PrintUnformatted(root);
  std::string out = text ? text : "{}";
  cJSON_free(text);
  cJSON_Delete(root);
  return out;
}

bool Settings::apply_json(const char *json, std::string &error, const char **code) {
  if (code) *code = "INVALID_JSON";
  cJSON *root = cJSON_Parse(json);
  if (!root) {
    error = "invalid JSON";
    return false;
  }
  if (!cJSON_IsObject(root)) {
    cJSON_Delete(root);
    error = "expected an object";
    return false;
  }
  // Read into a copy: a refused document leaves the settings as they were.
  Settings next = *this;
  const bool ordered = next.read_json(root);
  cJSON_Delete(root);
  if (!ordered) {
    if (code) *code = "INVALID_SETTINGS";
    error = "minimum artwork size " + std::to_string(snap_min_side(next.makapix_min_side)) + " above the maximum " +
            std::to_string(snap_max_side(next.makapix_max_side));
    return false;
  }
  *this = next;
  clamp();
  return true;
}

bool Settings::read_json(const cJSON *root) {
  const cJSON *d = sub(root, "display");
  get_num(d, "brightness", brightness);
  get_num(d, "brightness_ceiling", brightness_ceiling);
  const cJSON *n = sub(d, "night");
  get_bool(n, "enabled", night.enabled);
  get_num(n, "start_minutes", night.start_minutes);
  get_num(n, "end_minutes", night.end_minutes);
  get_num(n, "brightness", night.brightness);
  get_enum(d, "panel_mode", panel_mode, kPanelModes, 2);
  get_num(d, "rotation", rotation);
  get_bool(d, "rotation_auto", rotation_auto);
  get_bool(d, "mirror", mirror);
  get_rgb(d, "background", background);
  const cJSON *g = sub(d, "gains");
  get_num(g, "r", gain_r);
  get_num(g, "g", gain_g);
  get_num(g, "b", gain_b);
  get_num(d, "boot_animation_ms", boot_animation_ms);

  const cJSON *s = sub(root, "show");
  get_enum(s, "main_state", main_state, kMainStates, 3);
  get_num(s, "auto_swap_seconds", auto_swap_seconds);
  get_enum(s, "pick_mode", pick_mode, kPickModes, 2);
  get_enum(s, "channel_select", channel_select, kChannelSelects, 2);
  const cJSON *co = sub(s, "clock_overlay");
  get_bool(co, "enabled", clock_overlay.enabled);
  get_str(co, "font", clock_overlay.font, 32);
  get_enum(co, "corner", clock_overlay.corner, kCorners, sizeof(kCorners) / sizeof(kCorners[0]));
  get_bool(co, "h24", clock_overlay.h24);
  get_rgb(co, "colour", clock_overlay.colour);
  get_bool(co, "border", clock_overlay.border);
  get_rgb(co, "border_colour", clock_overlay.border_colour);
  get_num(co, "border_opacity", clock_overlay.border_opacity);

  const cJSON *w = sub(root, "widgets");
  get_enum(w, "widget", widget, kWidgets, sizeof(kWidgets) / sizeof(kWidgets[0]));
  const cJSON *ip = sub(w, "interlude_minutes");
  get_num(ip, "clock", interlude_clock);
  get_num(ip, "weather", interlude_weather);
  get_num(ip, "temperature", interlude_temperature);
  get_num(ip, "air", interlude_air);
  get_bool(w, "interlude_random_clock_face", interlude_random_clock_face);

  const cJSON *ck = sub(root, "clock");
  {
    get_enum(ck, "face", clock.face, kClockFaces, sizeof(kClockFaces) / sizeof(kClockFaces[0]));
    get_enum(ck, "led_style", clock.led_style, kLedStyles, sizeof(kLedStyles) / sizeof(kLedStyles[0]));
    get_str(ck, "font", clock.font, 32);
    get_num(ck, "scale", clock.scale);
    get_bool(ck, "seconds", clock.seconds);
    get_bool(ck, "blink_colon", clock.blink_colon);
    get_bool(ck, "h24", clock.h24);
    std::string order;
    get_str(ck, "date_order", order, 16);
    if (order == "month_day") clock.month_first = true;
    if (order == "day_month") clock.month_first = false;
    get_rgb(ck, "colour", clock.colour);
    get_rgb(ck, "background", clock.background);
  }
  const cJSON *we = sub(root, "weather");
  {
    const cJSON *lat = we ? cJSON_GetObjectItemCaseSensitive(we, "latitude") : nullptr;
    const cJSON *lon = we ? cJSON_GetObjectItemCaseSensitive(we, "longitude") : nullptr;
    if (lat && cJSON_IsNumber(lat) && lon && cJSON_IsNumber(lon)) {
      weather.latitude = static_cast<float>(lat->valuedouble);
      weather.longitude = static_cast<float>(lon->valuedouble);
      weather.location_set = true;
    }
    get_bool(we, "location_set", weather.location_set);
    std::string units;
    get_str(we, "units", units, 16);
    if (units == "imperial") weather.imperial = true;
    if (units == "metric") weather.imperial = false;
    get_num(we, "refresh_minutes", weather.refresh_minutes);
  }
  const cJSON *ai = sub(root, "air");
  {
    std::string index;
    get_str(ai, "index", index, 16);
    if (index == "european") air.european = true;
    if (index == "us") air.european = false;
  }
  const cJSON *te = sub(root, "temperature");
  get_num(te, "offset_temperature", temperature.offset_temperature);
  get_num(te, "offset_humidity", temperature.offset_humidity);
  get_bool(te, "trend", temperature.trend);

  const cJSON *st = sub(root, "stream");
  get_bool(st, "takeover", stream_takeover);
  get_num(st, "silence_ms", stream_silence_ms);
  get_bool(st, "ddp_enabled", ddp_enabled);
  get_num(st, "ddp_port", ddp_port);
  get_bool(st, "raw_udp_enabled", raw_udp_enabled);
  get_num(st, "raw_udp_port", raw_udp_port);

  const cJSON *in = sub(root, "inputs");
  get_bool(in, "tap_enabled", tap_enabled);
  get_num(in, "tap_sensitivity", tap_sensitivity);
  get_bool(in, "encoders_enabled", encoders_enabled);
  get_bool(in, "encoders_swap", encoders_swap);
  get_bool(in, "encoders_invert", encoders_invert);

  const cJSON *net = sub(root, "network");
  get_str(net, "device_name", device_name, 16);
  get_str(net, "timezone", timezone, 64);
  get_str(net, "ntp_server", ntp_server, 64);

  const cJSON *sto = sub(root, "storage");
  get_str(sto, "card_root", card_root, 64);
  get_num(sto, "downloads_cap_mb", downloads_cap_mb);

  const cJSON *mk = sub(root, "makapix");
  get_num(mk, "refresh_seconds", makapix_refresh_seconds);
  get_num(mk, "channel_cache_size", channel_cache_size);
  get_num(mk, "min_size", makapix_min_side);
  get_num(mk, "max_size", makapix_max_side);
  get_num(mk, "cache_retention_days", cache_retention_days);

  const cJSON *up = sub(root, "updates");
  get_bool(up, "auto_check", auto_update_check);

  // The one pair that can conflict: both sides of an artwork must be at least the
  // minimum and at most the maximum, so the steps must be ordered.
  return snap_min_side(makapix_min_side) <= snap_max_side(makapix_max_side);
}

}  // namespace p64::system
