fabkury/p64/firmware/components/esp-hub75/src/platforms/gdma/p64_bcm.h

// p64 patch: the bit-plane arithmetic of the p64 refresh profiles as pure code, so the
// host tests can check it (tests/host/unit/bcm.cpp; review of 2026-09-22). GdmaDma calls
// these; nothing here touches the hardware.
//
// A plane above the transition bit is sent 2^(bit - transition - 1) times per frame with
// the full output-enable window; a plane at or below it is sent once with half the window
// of the plane above, which restores its binary weight. A plane's weight is its window
// (pixel clocks) times its repetitions. The LUT maps each 8-bit input to the code whose
// weight is nearest the gamma table's target, which only works when the weights are
// superincreasing (each plane weighs at least the planes below it together): ten planes
// at transition bit 6 broke that on 2026-09-20 and every input above 13 mapped to code 3.
#pragma once

#include <algorithm>
#include <cmath>
#include <cstdint>

namespace hub75::p64bcm {

inline uint32_t plane_reps(int bit, int transition_bit) {
  return bit <= transition_bit ? 1u : (1u << (bit - transition_bit - 1));
}

// The output-enable window of each of `planes` planes, in pixel clocks, for a row of
// `max_pixels` usable clocks at `effective_brightness` (0..255 after the driver's curve).
// Keeps the weights superincreasing: a plane that would weigh less than the planes below
// it is blanked (it still costs its transmission).
//
// `round_low` rounds the halved windows of the planes sent once to the nearest clock
// instead of truncating them (2026-10-02, the eleven-plane trial): at transition bit 5
// the truncated windows are 0 1 3 7 15 31, plane 0 falls back to one clock and two
// planes weigh the same (239 codes); rounded they are 1 2 4 8 16 31, binary from one
// clock (243 codes). Quality and Photo keep the truncated windows they shipped with.
// Rounded up, the low windows can outweigh a plane sent several times, which would then be
// blanked (seen in the host tests at twelve planes, transition bit 9, half brightness);
// such a level falls back to the truncated windows.
inline void plane_windows(int max_pixels, int effective_brightness, int planes, int transition_bit, int out[],
                          bool round_low = false) {
  uint32_t weight_below = 0;
  for (int bit = 0; bit < planes; bit++) {
    int display_pixels = (max_pixels * effective_brightness) >> 8;
    if (bit <= transition_bit) {
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
